lerouxb/minor-1/firmware/attiny3216/include/avr/iotn3216.h

/*
 * Copyright (C) 2020, Microchip Technology Inc. and its subsidiaries ("Microchip")
 * All rights reserved.
 *
 * This software is developed by Microchip Technology Inc. and its subsidiaries ("Microchip").
 *
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
 *     3. Microchip's name may not be used to endorse or promote products derived from this
 *        software without specific prior written permission.
 *
 * THIS SOFTWARE IS PROVIDED BY MICROCHIP "AS IS" AND ANY EXPRESS OR IMPLIED WARRANTIES,
 * INCLUDING, BUT NOT LIMITED TO, THE IMPLIED WARRANTIES OF MERCHANTABILITY AND FITNESS FOR
 * PURPOSE ARE DISCLAIMED.  IN NO EVENT SHALL MICROCHIP BE LIABLE FOR ANY DIRECT, INDIRECT,
 * INCIDENTAL, SPECIAL, EXEMPLARY, OR CONSEQUENTIAL DAMAGES (INCLUDING BUT NOT LIMITED TO
 * PROCUREMENT OF SUBSTITUTE GOODS OR SERVICES; LOSS OF USE, DATA OR PROFITS; OR BUSINESS
 * INTERRUPTION) HOWSOEVER CAUSED AND ON ANY THEORY OF LIABILITY, WHETHER IN CONTRACT, STRICT
 * LIABILITY, OR TORT (INCLUDING NEGLIGENCE OR OTHERWISE) ARISING IN ANY WAY OUT OF THE USE OF
 * THIS SOFTWARE, EVEN IF ADVISED OF THE POSSIBILITY OF SUCH DAMAGE.
 */

#ifndef _AVR_IO_H_
#error "Include <avr/io.h> instead of this file."
#endif

#ifndef _AVR_IOXXX_H_
#define _AVR_IOXXX_H_ "iotn3216.h"
#else
#error "Attempt to include more than one <avr/ioXXX.h> file."
#endif

#ifndef _AVR_ATTINY3216_H_INCLUDED
#define _AVR_ATTINY3216_H_INCLUDED

/* Ungrouped common registers */
#define CCP _SFR_MEM8(0x0034)  /* Configuration Change Protection */
#define SPH _SFR_MEM8(0x003E)  /* Stack Pointer High */
#define SPL _SFR_MEM8(0x003D)  /* Stack Pointer Low */
#define SREG _SFR_MEM8(0x003F) /* Status Register */

#define GPIOR0 _SFR_MEM8(0x001C) /* General Purpose IO Register 0 */
#define GPIOR1 _SFR_MEM8(0x001D) /* General Purpose IO Register 1 */
#define GPIOR2 _SFR_MEM8(0x001E) /* General Purpose IO Register 2 */
#define GPIOR3 _SFR_MEM8(0x001F) /* General Purpose IO Register 3 */

/* Deprecated */
#define GPIO0 _SFR_MEM8(0x001C) /* General Purpose IO Register 0 */
#define GPIO1 _SFR_MEM8(0x001D) /* General Purpose IO Register 1 */
#define GPIO2 _SFR_MEM8(0x001E) /* General Purpose IO Register 2 */
#define GPIO3 _SFR_MEM8(0x001F) /* General Purpose IO Register 3 */

/* C Language Only */
#if !defined(__ASSEMBLER__)

#include <stdint.h>

typedef volatile uint8_t  register8_t;
typedef volatile uint16_t register16_t;
typedef volatile uint32_t register32_t;

#ifdef _WORDREGISTER
#undef _WORDREGISTER
#endif
#define _WORDREGISTER(regname)                                                                                         \
	__extension__ union {                                                                                              \
		register16_t regname;                                                                                          \
		struct {                                                                                                       \
			register8_t regname##L;                                                                                    \
			register8_t regname##H;                                                                                    \
		};                                                                                                             \
	}

#ifdef _DWORDREGISTER
#undef _DWORDREGISTER
#endif
#define _DWORDREGISTER(regname)                                                                                        \
	__extension__ union {                                                                                              \
		register32_t regname;                                                                                          \
		struct {                                                                                                       \
			register8_t regname##0;                                                                                    \
			register8_t regname##1;                                                                                    \
			register8_t regname##2;                                                                                    \
			register8_t regname##3;                                                                                    \
		};                                                                                                             \
	}

/*
==========================================================================
IO Module Structures
==========================================================================
*/

/*
--------------------------------------------------------------------------
AC - Analog Comparator
--------------------------------------------------------------------------
*/

/* Analog Comparator */
typedef struct AC_struct {
	register8_t CTRLA; /* Control A */
	register8_t reserved_1[1];
	register8_t MUXCTRLA; /* Mux Control A */
	register8_t reserved_2[3];
	register8_t INTCTRL; /* Interrupt Control */
	register8_t STATUS;  /* Status */
} AC_t;

/* Hysteresis Mode select */
typedef enum AC_HYSMODE_enum {
	AC_HYSMODE_OFF_gc  = (0x00 << 1), /* No hysteresis */
	AC_HYSMODE_10mV_gc = (0x01 << 1), /* 10mV hysteresis */
	AC_HYSMODE_25mV_gc = (0x02 << 1), /* 25mV hysteresis */
	AC_HYSMODE_50mV_gc = (0x03 << 1), /* 50mV hysteresis */
} AC_HYSMODE_t;

/* Interrupt Mode select */
typedef enum AC_INTMODE_enum {
	AC_INTMODE_BOTHEDGE_gc = (0x00 << 4), /* Any Edge */
	AC_INTMODE_NEGEDGE_gc  = (0x02 << 4), /* Negative Edge */
	AC_INTMODE_POSEDGE_gc  = (0x03 << 4), /* Positive Edge */
} AC_INTMODE_t;

/* Low Power Mode select */
typedef enum AC_LPMODE_enum {
	AC_LPMODE_DIS_gc = (0x00 << 3), /* Low power mode disabled */
	AC_LPMODE_EN_gc  = (0x01 << 3), /* Low power mode enabled */
} AC_LPMODE_t;

/* Negative Input MUX Selection select */
typedef enum AC_MUXNEG_enum {
	AC_MUXNEG_PIN0_gc = (0x00 << 0), /* Negative Pin 0 */
	AC_MUXNEG_PIN1_gc = (0x01 << 0), /* Negative Pin 1 */
	AC_MUXNEG_VREF_gc = (0x02 << 0), /* Voltage Reference */
	AC_MUXNEG_DAC_gc  = (0x03 << 0), /* DAC output */
} AC_MUXNEG_t;

/* Positive Input MUX Selection select */
typedef enum AC_MUXPOS_enum {
	AC_MUXPOS_PIN0_gc = (0x00 << 3), /* Positive Pin 0 */
	AC_MUXPOS_PIN1_gc = (0x01 << 3), /* Positive Pin 1 */
	AC_MUXPOS_PIN2_gc = (0x02 << 3), /* Positive Pin 2 */
	AC_MUXPOS_PIN3_gc = (0x03 << 3), /* Positive Pin 3 */
} AC_MUXPOS_t;

/*
--------------------------------------------------------------------------
ADC - Analog to Digital Converter
--------------------------------------------------------------------------
*/

/* Analog to Digital Converter */
typedef struct ADC_struct {
	register8_t CTRLA;    /* Control A */
	register8_t CTRLB;    /* Control B */
	register8_t CTRLC;    /* Control C */
	register8_t CTRLD;    /* Control D */
	register8_t CTRLE;    /* Control E */
	register8_t SAMPCTRL; /* Sample Control */
	register8_t MUXPOS;   /* Positive mux input */
	register8_t reserved_1[1];
	register8_t COMMAND;  /* Command */
	register8_t EVCTRL;   /* Event Control */
	register8_t INTCTRL;  /* Interrupt Control */
	register8_t INTFLAGS; /* Interrupt Flags */
	register8_t DBGCTRL;  /* Debug Control */
	register8_t TEMP;     /* Temporary Data */
	register8_t reserved_2[2];
	_WORDREGISTER(RES);   /* ADC Accumulator Result */
	_WORDREGISTER(WINLT); /* Window comparator low threshold */
	_WORDREGISTER(WINHT); /* Window comparator high threshold */
	register8_t CALIB;    /* Calibration */
	register8_t reserved_3[1];
} ADC_t;

/* Automatic Sampling Delay Variation select */
typedef enum ADC_ASDV_enum {
	ADC_ASDV_ASVOFF_gc = (0x00 << 4), /* The Automatic Sampling Delay Variation is disabled */
	ADC_ASDV_ASVON_gc  = (0x01 << 4), /* The Automatic Sampling Delay Variation is enabled */
} ADC_ASDV_t;

/* Duty Cycle select */
typedef enum ADC_DUTYCYC_enum {
	ADC_DUTYCYC_DUTY50_gc = (0x00 << 0), /* 50% Duty cycle */
	ADC_DUTYCYC_DUTY25_gc = (0x01 << 0), /* 25% Duty cycle */
} ADC_DUTYCYC_t;

/* Initial Delay Selection select */
typedef enum ADC_INITDLY_enum {
	ADC_INITDLY_DLY0_gc   = (0x00 << 5), /* Delay 0 CLK_ADC cycles */
	ADC_INITDLY_DLY16_gc  = (0x01 << 5), /* Delay 16 CLK_ADC cycles */
	ADC_INITDLY_DLY32_gc  = (0x02 << 5), /* Delay 32 CLK_ADC cycles */
	ADC_INITDLY_DLY64_gc  = (0x03 << 5), /* Delay 64 CLK_ADC cycles */
	ADC_INITDLY_DLY128_gc = (0x04 << 5), /* Delay 128 CLK_ADC cycles */
	ADC_INITDLY_DLY256_gc = (0x05 << 5), /* Delay 256 CLK_ADC cycles */
} ADC_INITDLY_t;

/* Analog Channel Selection Bits select */
typedef enum ADC_MUXPOS_enum {
	ADC_MUXPOS_AIN0_gc      = (0x00 << 0), /* ADC input pin 0 */
	ADC_MUXPOS_AIN1_gc      = (0x01 << 0), /* ADC input pin 1 */
	ADC_MUXPOS_AIN2_gc      = (0x02 << 0), /* ADC input pin 2 */
	ADC_MUXPOS_AIN3_gc      = (0x03 << 0), /* ADC input pin 3 */
	ADC_MUXPOS_AIN4_gc      = (0x04 << 0), /* ADC input pin 4 */
	ADC_MUXPOS_AIN5_gc      = (0x05 << 0), /* ADC input pin 5 */
	ADC_MUXPOS_AIN6_gc      = (0x06 << 0), /* ADC input pin 6 */
	ADC_MUXPOS_AIN7_gc      = (0x07 << 0), /* ADC input pin 7 */
	ADC_MUXPOS_AIN8_gc      = (0x08 << 0), /* ADC input pin 8 */
	ADC_MUXPOS_AIN9_gc      = (0x09 << 0), /* ADC input pin 9 */
	ADC_MUXPOS_AIN10_gc     = (0x0A << 0), /* ADC input pin 10 */
	ADC_MUXPOS_AIN11_gc     = (0x0B << 0), /* ADC input pin 11 */
	ADC_MUXPOS_PTC_gc       = (0x1B << 0), /* PTC/DAC2 */
	ADC_MUXPOS_DAC0_gc      = (0x1C << 0), /* DAC0/DAC0 */
	ADC_MUXPOS_INTREF_gc    = (0x1D << 0), /* Internal Ref */
	ADC_MUXPOS_TEMPSENSE_gc = (0x1E << 0), /* Temp sensor/DAC1 */
	ADC_MUXPOS_GND_gc       = (0x1F << 0), /* GND */
} ADC_MUXPOS_t;

/* Clock Pre-scaler select */
typedef enum ADC_PRESC_enum {
	ADC_PRESC_DIV2_gc   = (0x00 << 0), /* CLK_PER divided by 2 */
	ADC_PRESC_DIV4_gc   = (0x01 << 0), /* CLK_PER divided by 4 */
	ADC_PRESC_DIV8_gc   = (0x02 << 0), /* CLK_PER divided by 8 */
	ADC_PRESC_DIV16_gc  = (0x03 << 0), /* CLK_PER divided by 16 */
	ADC_PRESC_DIV32_gc  = (0x04 << 0), /* CLK_PER divided by 32 */
	ADC_PRESC_DIV64_gc  = (0x05 << 0), /* CLK_PER divided by 64 */
	ADC_PRESC_DIV128_gc = (0x06 << 0), /* CLK_PER divided by 128 */
	ADC_PRESC_DIV256_gc = (0x07 << 0), /* CLK_PER divided by 256 */
} ADC_PRESC_t;

/* Reference Selection select */
typedef enum ADC_REFSEL_enum {
	ADC_REFSEL_INTREF_gc = (0x00 << 4), /* Internal reference */
	ADC_REFSEL_VDDREF_gc = (0x01 << 4), /* VDD */
	ADC_REFSEL_VREFA_gc  = (0x02 << 4), /* External reference */
} ADC_REFSEL_t;

/* ADC Resolution select */
typedef enum ADC_RESSEL_enum {
	ADC_RESSEL_10BIT_gc = (0x00 << 2), /* 10-bit mode */
	ADC_RESSEL_8BIT_gc  = (0x01 << 2), /* 8-bit mode */
} ADC_RESSEL_t;

/* Accumulation Samples select */
typedef enum ADC_SAMPNUM_enum {
	ADC_SAMPNUM_ACC1_gc  = (0x00 << 0), /* 1 ADC sample */
	ADC_SAMPNUM_ACC2_gc  = (0x01 << 0), /* Accumulate 2 samples */
	ADC_SAMPNUM_ACC4_gc  = (0x02 << 0), /* Accumulate 4 samples */
	ADC_SAMPNUM_ACC8_gc  = (0x03 << 0), /* Accumulate 8 samples */
	ADC_SAMPNUM_ACC16_gc = (0x04 << 0), /* Accumulate 16 samples */
	ADC_SAMPNUM_ACC32_gc = (0x05 << 0), /* Accumulate 32 samples */
	ADC_SAMPNUM_ACC64_gc = (0x06 << 0), /* Accumulate 64 samples */
} ADC_SAMPNUM_t;

/* Window Comparator Mode select */
typedef enum ADC_WINCM_enum {
	ADC_WINCM_NONE_gc    = (0x00 << 0), /* No Window Comparison */
	ADC_WINCM_BELOW_gc   = (0x01 << 0), /* Below Window */
	ADC_WINCM_ABOVE_gc   = (0x02 << 0), /* Above Window */
	ADC_WINCM_INSIDE_gc  = (0x03 << 0), /* Inside Window */
	ADC_WINCM_OUTSIDE_gc = (0x04 << 0), /* Outside Window */
} ADC_WINCM_t;

/*
--------------------------------------------------------------------------
BOD - Bod interface
--------------------------------------------------------------------------
*/

/* Bod interface */
typedef struct BOD_struct {
	register8_t CTRLA; /* Control A */
	register8_t CTRLB; /* Control B */
	register8_t reserved_1[6];
	register8_t VLMCTRLA; /* Voltage level monitor Control */
	register8_t INTCTRL;  /* Voltage level monitor interrupt Control */
	register8_t INTFLAGS; /* Voltage level monitor interrupt Flags */
	register8_t STATUS;   /* Voltage level monitor status */
	register8_t reserved_2[4];
} BOD_t;

/* Operation in active mode select */
typedef enum BOD_ACTIVE_enum {
	BOD_ACTIVE_DIS_gc     = (0x00 << 2), /* Disabled */
	BOD_ACTIVE_ENABLED_gc = (0x01 << 2), /* Enabled */
	BOD_ACTIVE_SAMPLED_gc = (0x02 << 2), /* Sampled */
	BOD_ACTIVE_ENWAKE_gc  = (0x03 << 2), /* Enabled with wake-up halted until BOD is ready */
} BOD_ACTIVE_t;

/* Bod level select */
typedef enum BOD_LVL_enum {
	BOD_LVL_BODLEVEL0_gc = (0x00 << 0), /* 1.8 V */
	BOD_LVL_BODLEVEL2_gc = (0x02 << 0), /* 2.6 V */
	BOD_LVL_BODLEVEL7_gc = (0x07 << 0), /* 4.2 V */
} BOD_LVL_t;

/* Sample frequency select */
typedef enum BOD_SAMPFREQ_enum {
	BOD_SAMPFREQ_1KHZ_gc  = (0x00 << 4), /* 1kHz sampling frequency */
	BOD_SAMPFREQ_125HZ_gc = (0x01 << 4), /* 125Hz sampling frequency */
} BOD_SAMPFREQ_t;

/* Operation in sleep mode select */
typedef enum BOD_SLEEP_enum {
	BOD_SLEEP_DIS_gc     = (0x00 << 0), /* Disabled */
	BOD_SLEEP_ENABLED_gc = (0x01 << 0), /* Enabled */
	BOD_SLEEP_SAMPLED_gc = (0x02 << 0), /* Sampled */
} BOD_SLEEP_t;

/* Configuration select */
typedef enum BOD_VLMCFG_enum {
	BOD_VLMCFG_BELOW_gc = (0x00 << 1), /* Interrupt when supply goes below VLM level */
	BOD_VLMCFG_ABOVE_gc = (0x01 << 1), /* Interrupt when supply goes above VLM level */
	BOD_VLMCFG_CROSS_gc = (0x02 << 1), /* Interrupt when supply crosses VLM level */
} BOD_VLMCFG_t;

/* voltage level monitor level select */
typedef enum BOD_VLMLVL_enum {
	BOD_VLMLVL_5ABOVE_gc  = (0x00 << 0), /* VLM threshold 5% above BOD level */
	BOD_VLMLVL_15ABOVE_gc = (0x01 << 0), /* VLM threshold 15% above BOD level */
	BOD_VLMLVL_25ABOVE_gc = (0x02 << 0), /* VLM threshold 25% above BOD level */
} BOD_VLMLVL_t;

/*
--------------------------------------------------------------------------
CCL - Configurable Custom Logic
--------------------------------------------------------------------------
*/

/* Configurable Custom Logic */
typedef struct CCL_struct {
	register8_t CTRLA;    /* Control Register A */
	register8_t SEQCTRL0; /* Sequential Control 0 */
	register8_t reserved_1[3];
	register8_t LUT0CTRLA; /* LUT Control 0 A */
	register8_t LUT0CTRLB; /* LUT Control 0 B */
	register8_t LUT0CTRLC; /* LUT Control 0 C */
	register8_t TRUTH0;    /* Truth 0 */
	register8_t LUT1CTRLA; /* LUT Control 1 A */
	register8_t LUT1CTRLB; /* LUT Control 1 B */
	register8_t LUT1CTRLC; /* LUT Control 1 C */
	register8_t TRUTH1;    /* Truth 1 */
	register8_t reserved_2[51];
} CCL_t;

/* Edge Detection Enable select */
typedef enum CCL_EDGEDET_enum {
	CCL_EDGEDET_DIS_gc = (0x00 << 7), /* Edge detector is disabled */
	CCL_EDGEDET_EN_gc  = (0x01 << 7), /* Edge detector is enabled */
} CCL_EDGEDET_t;

/* Filter Selection select */
typedef enum CCL_FILTSEL_enum {
	CCL_FILTSEL_DISABLE_gc = (0x00 << 4), /* Filter disabled */
	CCL_FILTSEL_SYNCH_gc   = (0x01 << 4), /* Synchronizer enabled */
	CCL_FILTSEL_FILTER_gc  = (0x02 << 4), /* Filter enabled */
} CCL_FILTSEL_t;

/* LUT Input 0 Source Selection select */
typedef enum CCL_INSEL0_enum {
	CCL_INSEL0_MASK_gc     = (0x00 << 0), /* Masked input */
	CCL_INSEL0_FEEDBACK_gc = (0x01 << 0), /* Feedback input source */
	CCL_INSEL0_LINK_gc     = (0x02 << 0), /* Linked LUT input source */
	CCL_INSEL0_EVENT0_gc   = (0x03 << 0), /* Event input source 0 */
	CCL_INSEL0_EVENT1_gc   = (0x04 << 0), /* Event input source 1 */
	CCL_INSEL0_IO_gc       = (0x05 << 0), /* IO pin LUTn-IN0 input source */
	CCL_INSEL0_AC0_gc      = (0x06 << 0), /* AC0 OUT input source */
	CCL_INSEL0_TCB0_gc     = (0x07 << 0), /* TCB0 WO input source */
	CCL_INSEL0_TCA0_gc     = (0x08 << 0), /* TCA0 WO0 input source */
	CCL_INSEL0_TCD0_gc     = (0x09 << 0), /* TCD0 WOA input source */
	CCL_INSEL0_USART0_gc   = (0x0A << 0), /* USART0 XCK input source */
	CCL_INSEL0_SPI0_gc     = (0x0B << 0), /* SPI0 SCK source */
	CCL_INSEL0_AC1_gc      = (0x0C << 0), /* AC1 OUT input source */
	CCL_INSEL0_TCB1_gc     = (0x0D << 0), /* TCB1 WO input source */
	CCL_INSEL0_AC2_gc      = (0x0E << 0), /* AC2 OUT input source */
} CCL_INSEL0_t;

/* LUT Input 1 Source Selection select */
typedef enum CCL_INSEL1_enum {
	CCL_INSEL1_MASK_gc     = (0x00 << 4), /* Masked input */
	CCL_INSEL1_FEEDBACK_gc = (0x01 << 4), /* Feedback input source */
	CCL_INSEL1_LINK_gc     = (0x02 << 4), /* Linked LUT input source */
	CCL_INSEL1_EVENT0_gc   = (0x03 << 4), /* Event input source 0 */
	CCL_INSEL1_EVENT1_gc   = (0x04 << 4), /* Event input source 1 */
	CCL_INSEL1_IO_gc       = (0x05 << 4), /* IO pin LUTn-N1 input source */
	CCL_INSEL1_AC0_gc      = (0x06 << 4), /* AC0 OUT input source */
	CCL_INSEL1_TCB0_gc     = (0x07 << 4), /* TCB0 WO input source */
	CCL_INSEL1_TCA0_gc     = (0x08 << 4), /* TCA0 WO1 input source */
	CCL_INSEL1_TCD0_gc     = (0x09 << 4), /* TCD0 WOB input source */
	CCL_INSEL1_USART0_gc   = (0x0A << 4), /* USART0 TXD input source */
	CCL_INSEL1_SPI0_gc     = (0x0B << 4), /* SPI0 MOSI input source */
	CCL_INSEL1_AC1_gc      = (0x0C << 4), /* AC1 OUT input source */
	CCL_INSEL1_TCB1_gc     = (0x0D << 4), /* TCB1 WO input source */
	CCL_INSEL1_AC2_gc      = (0x0E << 4), /* AC2 OUT input source */
} CCL_INSEL1_t;

/* LUT Input 2 Source Selection select */
typedef enum CCL_INSEL2_enum {
	CCL_INSEL2_MASK_gc     = (0x00 << 0), /* Masked input */
	CCL_INSEL2_FEEDBACK_gc = (0x01 << 0), /* Feedback input source */
	CCL_INSEL2_LINK_gc     = (0x02 << 0), /* Linked LUT input source */
	CCL_INSEL2_EVENT0_gc   = (0x03 << 0), /* Event input source 0 */
	CCL_INSEL2_EVENT1_gc   = (0x04 << 0), /* Event input source 1 */
	CCL_INSEL2_IO_gc       = (0x05 << 0), /* IO pin LUTn-IN2 input source */
	CCL_INSEL2_AC0_gc      = (0x06 << 0), /* AC0 OUT input source */
	CCL_INSEL2_TCB0_gc     = (0x07 << 0), /* TCB0 WO input source */
	CCL_INSEL2_TCA0_gc     = (0x08 << 0), /* TCA0 WO2 input source */
	CCL_INSEL2_TCD0_gc     = (0x09 << 0), /* TCD0 WOA input source */
	CCL_INSEL2_SPI0_gc     = (0x0B << 0), /* SPI0 MISO source */
	CCL_INSEL2_AC1_gc      = (0x0C << 0), /* AC1 OUT input source */
	CCL_INSEL2_TCB1_gc     = (0x0D << 0), /* TCB1 WO input source */
	CCL_INSEL2_AC2_gc      = (0x0E << 0), /* AC2 OUT input source */
} CCL_INSEL2_t;

/* Sequential Selection select */
typedef enum CCL_SEQSEL_enum {
	CCL_SEQSEL_DISABLE_gc = (0x00 << 0), /* Sequential logic disabled */
	CCL_SEQSEL_DFF_gc     = (0x01 << 0), /* D FlipFlop */
	CCL_SEQSEL_JK_gc      = (0x02 << 0), /* JK FlipFlop */
	CCL_SEQSEL_LATCH_gc   = (0x03 << 0), /* D Latch */
	CCL_SEQSEL_RS_gc      = (0x04 << 0), /* RS Latch */
} CCL_SEQSEL_t;

/*
--------------------------------------------------------------------------
CLKCTRL - Clock controller
--------------------------------------------------------------------------
*/

/* Clock controller */
typedef struct CLKCTRL_struct {
	register8_t MCLKCTRLA;  /* MCLK Control A */
	register8_t MCLKCTRLB;  /* MCLK Control B */
	register8_t MCLKLOCK;   /* MCLK Lock */
	register8_t MCLKSTATUS; /* MCLK Status */
	register8_t reserved_1[12];
	register8_t OSC20MCTRLA;  /* OSC20M Control A */
	register8_t OSC20MCALIBA; /* OSC20M Calibration A */
	register8_t OSC20MCALIBB; /* OSC20M Calibration B */
	register8_t reserved_2[5];
	register8_t OSC32KCTRLA; /* OSC32K Control A */
	register8_t reserved_3[3];
	register8_t XOSC32KCTRLA; /* XOSC32K Control A */
	register8_t reserved_4[3];
} CLKCTRL_t;

/* clock select select */
typedef enum CLKCTRL_CLKSEL_enum {
	CLKCTRL_CLKSEL_OSC20M_gc    = (0x00 << 0), /* 20MHz internal oscillator */
	CLKCTRL_CLKSEL_OSCULP32K_gc = (0x01 << 0), /* 32KHz internal Ultra Low Power oscillator */
	CLKCTRL_CLKSEL_XOSC32K_gc   = (0x02 << 0), /* 32.768kHz external crystal oscillator */
	CLKCTRL_CLKSEL_EXTCLK_gc    = (0x03 << 0), /* External clock */
} CLKCTRL_CLKSEL_t;

/* Crystal startup time select */
typedef enum CLKCTRL_CSUT_enum {
	CLKCTRL_CSUT_1K_gc  = (0x00 << 4), /* 1K cycles */
	CLKCTRL_CSUT_16K_gc = (0x01 << 4), /* 16K cycles */
	CLKCTRL_CSUT_32K_gc = (0x02 << 4), /* 32K cycles */
	CLKCTRL_CSUT_64K_gc = (0x03 << 4), /* 64K cycles */
} CLKCTRL_CSUT_t;

/* Prescaler division select */
typedef enum CLKCTRL_PDIV_enum {
	CLKCTRL_PDIV_2X_gc  = (0x00 << 1), /* 2X */
	CLKCTRL_PDIV_4X_gc  = (0x01 << 1), /* 4X */
	CLKCTRL_PDIV_8X_gc  = (0x02 << 1), /* 8X */
	CLKCTRL_PDIV_16X_gc = (0x03 << 1), /* 16X */
	CLKCTRL_PDIV_32X_gc = (0x04 << 1), /* 32X */
	CLKCTRL_PDIV_64X_gc = (0x05 << 1), /* 64X */
	CLKCTRL_PDIV_6X_gc  = (0x08 << 1), /* 6X */
	CLKCTRL_PDIV_10X_gc = (0x09 << 1), /* 10X */
	CLKCTRL_PDIV_12X_gc = (0x0A << 1), /* 12X */
	CLKCTRL_PDIV_24X_gc = (0x0B << 1), /* 24X */
	CLKCTRL_PDIV_48X_gc = (0x0C << 1), /* 48X */
} CLKCTRL_PDIV_t;

/*
--------------------------------------------------------------------------
CPU - CPU
--------------------------------------------------------------------------
*/

/* CCP signature select */
typedef enum CCP_enum {
	CCP_SPM_gc   = (0x9D << 0), /* SPM Instruction Protection */
	CCP_IOREG_gc = (0xD8 << 0), /* IO Register Protection */
} CCP_t;

/*
--------------------------------------------------------------------------
CPUINT - Interrupt Controller
--------------------------------------------------------------------------
*/

/* Interrupt Controller */
typedef struct CPUINT_struct {
	register8_t CTRLA;   /* Control A */
	register8_t STATUS;  /* Status */
	register8_t LVL0PRI; /* Interrupt Level 0 Priority */
	register8_t LVL1VEC; /* Interrupt Level 1 Priority Vector */
} CPUINT_t;

/*
--------------------------------------------------------------------------
CRCSCAN - CRCSCAN
--------------------------------------------------------------------------
*/

/* CRCSCAN */
typedef struct CRCSCAN_struct {
	register8_t CTRLA;  /* Control A */
	register8_t CTRLB;  /* Control B */
	register8_t STATUS; /* Status */
	register8_t reserved_1[1];
} CRCSCAN_t;

/* CRC Source select */
typedef enum CRCSCAN_SRC_enum {
	CRCSCAN_SRC_FLASH_gc       = (0x00 << 0), /* CRC on entire flash */
	CRCSCAN_SRC_APPLICATION_gc = (0x01 << 0), /* CRC on boot and appl section of flash */
	CRCSCAN_SRC_BOOT_gc        = (0x02 << 0), /* CRC on boot section of flash */
} CRCSCAN_SRC_t;

/*
--------------------------------------------------------------------------
DAC - Digital to Analog Converter
--------------------------------------------------------------------------
*/

/* Digital to Analog Converter */
typedef struct DAC_struct {
	register8_t CTRLA; /* Control Register A */
	register8_t DATA;  /* DATA Register */
	register8_t reserved_1[2];
} DAC_t;

/*
--------------------------------------------------------------------------
EVSYS - Event System
--------------------------------------------------------------------------
*/

/* Event System */
typedef struct EVSYS_struct {
	register8_t ASYNCSTROBE; /* Asynchronous Channel Strobe */
	register8_t SYNCSTROBE;  /* Synchronous Channel Strobe */
	register8_t ASYNCCH0;    /* Asynchronous Channel 0 Generator Selection */
	register8_t ASYNCCH1;    /* Asynchronous Channel 1 Generator Selection */
	register8_t ASYNCCH2;    /* Asynchronous Channel 2 Generator Selection */
	register8_t ASYNCCH3;    /* Asynchronous Channel 3 Generator Selection */
	register8_t reserved_1[4];
	register8_t SYNCCH0; /* Synchronous Channel 0 Generator Selection */
	register8_t SYNCCH1; /* Synchronous Channel 1 Generator Selection */
	register8_t reserved_2[6];
	register8_t ASYNCUSER0;  /* Asynchronous User Ch 0 Input Selection - TCB0 */
	register8_t ASYNCUSER1;  /* Asynchronous User Ch 1 Input Selection - ADC0 */
	register8_t ASYNCUSER2;  /* Asynchronous User Ch 2 Input Selection - CCL LUT0 Event 0 */
	register8_t ASYNCUSER3;  /* Asynchronous User Ch 3 Input Selection - CCL LUT1 Event 0 */
	register8_t ASYNCUSER4;  /* Asynchronous User Ch 4 Input Selection - CCL LUT0 Event 1 */
	register8_t ASYNCUSER5;  /* Asynchronous User Ch 5 Input Selection - CCL LUT1 Event 1 */
	register8_t ASYNCUSER6;  /* Asynchronous User Ch 6 Input Selection - TCD0 Event 0 */
	register8_t ASYNCUSER7;  /* Asynchronous User Ch 7 Input Selection - TCD0 Event 1 */
	register8_t ASYNCUSER8;  /* Asynchronous User Ch 8 Input Selection - Event Out 0 */
	register8_t ASYNCUSER9;  /* Asynchronous User Ch 9 Input Selection - Event Out 1 */
	register8_t ASYNCUSER10; /* Asynchronous User Ch 10 Input Selection - Event Out 2 */
	register8_t ASYNCUSER11; /* Asynchronous User Ch 11 Input Selection - TCB1 */
	register8_t ASYNCUSER12; /* Asynchronous User Ch 12 Input Selection - ADC1 */
	register8_t reserved_3[3];
	register8_t SYNCUSER0; /* Synchronous User Ch 0 - TCA0 */
	register8_t SYNCUSER1; /* Synchronous User Ch 1 - USART0 */
	register8_t reserved_4[28];
} EVSYS_t;

/* Asynchronous Channel 0 Generator Selection select */
typedef enum EVSYS_ASYNCCH0_enum {
	EVSYS_ASYNCCH0_OFF_gc          = (0x00 << 0), /* Off */
	EVSYS_ASYNCCH0_CCL_LUT0_gc     = (0x01 << 0), /* Configurable Custom Logic LUT0 */
	EVSYS_ASYNCCH0_CCL_LUT1_gc     = (0x02 << 0), /* Configurable Custom Logic LUT1 */
	EVSYS_ASYNCCH0_AC0_OUT_gc      = (0x03 << 0), /* Analog Comparator 0 out */
	EVSYS_ASYNCCH0_TCD0_CMPBCLR_gc = (0x04 << 0), /* Timer/Counter D0 compare B clear */
	EVSYS_ASYNCCH0_TCD0_CMPASET_gc = (0x05 << 0), /* Timer/Counter D0 compare A set */
	EVSYS_ASYNCCH0_TCD0_CMPBSET_gc = (0x06 << 0), /* Timer/Counter D0 compare B set */
	EVSYS_ASYNCCH0_TCD0_PROGEV_gc  = (0x07 << 0), /* Timer/Counter D0 program event */
	EVSYS_ASYNCCH0_RTC_OVF_gc      = (0x08 << 0), /* Real Time Counter overflow */
	EVSYS_ASYNCCH0_RTC_CMP_gc      = (0x09 << 0), /* Real Time Counter compare */
	EVSYS_ASYNCCH0_PORTA_PIN0_gc   = (0x0A << 0), /* Asynchronous Event from Pin PA0 */
	EVSYS_ASYNCCH0_PORTA_PIN1_gc   = (0x0B << 0), /* Asynchronous Event from Pin PA1 */
	EVSYS_ASYNCCH0_PORTA_PIN2_gc   = (0x0C << 0), /* Asynchronous Event from Pin PA2 */
	EVSYS_ASYNCCH0_PORTA_PIN3_gc   = (0x0D << 0), /* Asynchronous Event from Pin PA3 */
	EVSYS_ASYNCCH0_PORTA_PIN4_gc   = (0x0E << 0), /* Asynchronous Event from Pin PA4 */
	EVSYS_ASYNCCH0_PORTA_PIN5_gc   = (0x0F << 0), /* Asynchronous Event from Pin PA5 */
	EVSYS_ASYNCCH0_PORTA_PIN6_gc   = (0x10 << 0), /* Asynchronous Event from Pin PA6 */
	EVSYS_ASYNCCH0_PORTA_PIN7_gc   = (0x11 << 0), /* Asynchronous Event from Pin PA7 */
	EVSYS_ASYNCCH0_UPDI_gc         = (0x12 << 0), /* Unified Program and debug interface */
	EVSYS_ASYNCCH0_AC1_OUT_gc      = (0x13 << 0), /* Analog Comparator 1 out */
	EVSYS_ASYNCCH0_AC2_OUT_gc      = (0x14 << 0), /* Analog Comparator 2 out */
} EVSYS_ASYNCCH0_t;

/* Asynchronous Channel 1 Generator Selection select */
typedef enum EVSYS_ASYNCCH1_enum {
	EVSYS_ASYNCCH1_OFF_gc          = (0x00 << 0), /* Off */
	EVSYS_ASYNCCH1_CCL_LUT0_gc     = (0x01 << 0), /* Configurable custom logic LUT0 */
	EVSYS_ASYNCCH1_CCL_LUT1_gc     = (0x02 << 0), /* Configurable custom logic LUT1 */
	EVSYS_ASYNCCH1_AC0_OUT_gc      = (0x03 << 0), /* Analog Comparator 0 out */
	EVSYS_ASYNCCH1_TCD0_CMPBCLR_gc = (0x04 << 0), /* Timer/Counter D0 compare B clear */
	EVSYS_ASYNCCH1_TCD0_CMPASET_gc = (0x05 << 0), /* Timer/Counter D0 compare A set */
	EVSYS_ASYNCCH1_TCD0_CMPBSET_gc = (0x06 << 0), /* Timer/Counter D0 compare B set */
	EVSYS_ASYNCCH1_TCD0_PROGEV_gc  = (0x07 << 0), /* Timer/Counter D0 program event */
	EVSYS_ASYNCCH1_RTC_OVF_gc      = (0x08 << 0), /* Real Time Counter overflow */
	EVSYS_ASYNCCH1_RTC_CMP_gc      = (0x09 << 0), /* Real Time Counter compare */
	EVSYS_ASYNCCH1_PORTB_PIN0_gc   = (0x0A << 0), /* Asynchronous Event from Pin PB0 */
	EVSYS_ASYNCCH1_PORTB_PIN1_gc   = (0x0B << 0), /* Asynchronous Event from Pin PB1 */
	EVSYS_ASYNCCH1_PORTB_PIN2_gc   = (0x0C << 0), /* Asynchronous Event from Pin PB2 */
	EVSYS_ASYNCCH1_PORTB_PIN3_gc   = (0x0D << 0), /* Asynchronous Event from Pin PB3 */
	EVSYS_ASYNCCH1_PORTB_PIN4_gc   = (0x0E << 0), /* Asynchronous Event from Pin PB4 */
	EVSYS_ASYNCCH1_PORTB_PIN5_gc   = (0x0F << 0), /* Asynchronous Event from Pin PB5 */
	EVSYS_ASYNCCH1_PORTB_PIN6_gc   = (0x10 << 0), /* Asynchronous Event from Pin PB6 */
	EVSYS_ASYNCCH1_PORTB_PIN7_gc   = (0x11 << 0), /* Asynchronous Event from Pin PB7 */
	EVSYS_ASYNCCH1_AC1_OUT_gc      = (0x12 << 0), /* Analog Comparator 1 out */
	EVSYS_ASYNCCH1_AC2_OUT_gc      = (0x13 << 0), /* Analog Comparator 2 out */
} EVSYS_ASYNCCH1_t;

/* Asynchronous Channel 2 Generator Selection select */
typedef enum EVSYS_ASYNCCH2_enum {
	EVSYS_ASYNCCH2_OFF_gc          = (0x00 << 0), /* Off */
	EVSYS_ASYNCCH2_CCL_LUT0_gc     = (0x01 << 0), /* Configurable Custom Logic LUT0 */
	EVSYS_ASYNCCH2_CCL_LUT1_gc     = (0x02 << 0), /* Configurable Custom Logic LUT1 */
	EVSYS_ASYNCCH2_AC0_OUT_gc      = (0x03 << 0), /* Analog Comparator 0 out */
	EVSYS_ASYNCCH2_TCD0_CMPBCLR_gc = (0x04 << 0), /* Timer/Counter D0 compare B clear */
	EVSYS_ASYNCCH2_TCD0_CMPASET_gc = (0x05 << 0), /* Timer/Counter D0 compare A set */
	EVSYS_ASYNCCH2_TCD0_CMPBSET_gc = (0x06 << 0), /* Timer/Counter D0 compare B set */
	EVSYS_ASYNCCH2_TCD0_PROGEV_gc  = (0x07 << 0), /* Timer/Counter D0 program event */
	EVSYS_ASYNCCH2_RTC_OVF_gc      = (0x08 << 0), /* Real Time Counter overflow */
	EVSYS_ASYNCCH2_RTC_CMP_gc      = (0x09 << 0), /* Real Time Counter compare */
	EVSYS_ASYNCCH2_PORTC_PIN0_gc   = (0x0A << 0), /* Asynchronous Event from Pin PC0 */
	EVSYS_ASYNCCH2_PORTC_PIN1_gc   = (0x0B << 0), /* Asynchronous Event from Pin PC1 */
	EVSYS_ASYNCCH2_PORTC_PIN2_gc   = (0x0C << 0), /* Asynchronous Event from Pin PC2 */
	EVSYS_ASYNCCH2_PORTC_PIN3_gc   = (0x0D << 0), /* Asynchronous Event from Pin PC3 */
	EVSYS_ASYNCCH2_PORTC_PIN4_gc   = (0x0E << 0), /* Asynchronous Event from Pin PC4 */
	EVSYS_ASYNCCH2_PORTC_PIN5_gc   = (0x0F << 0), /* Asynchronous Event from Pin PC5 */
	EVSYS_ASYNCCH2_AC1_OUT_gc      = (0x10 << 0), /* Analog Comparator 1 out */
	EVSYS_ASYNCCH2_AC2_OUT_gc      = (0x11 << 0), /* Analog Comparator 2 out */
} EVSYS_ASYNCCH2_t;

/* Asynchronous Channel 3 Generator Selection select */
typedef enum EVSYS_ASYNCCH3_enum {
	EVSYS_ASYNCCH3_OFF_gc          = (0x00 << 0), /* Off */
	EVSYS_ASYNCCH3_CCL_LUT0_gc     = (0x01 << 0), /* Configurable custom logic LUT0 */
	EVSYS_ASYNCCH3_CCL_LUT1_gc     = (0x02 << 0), /* Configurable custom logic LUT1 */
	EVSYS_ASYNCCH3_AC0_OUT_gc      = (0x03 << 0), /* Analog Comparator 0 out */
	EVSYS_ASYNCCH3_TCD0_CMPBCLR_gc = (0x04 << 0), /* Timer/Counter type D compare B clear */
	EVSYS_ASYNCCH3_TCD0_CMPASET_gc = (0x05 << 0), /* Timer/Counter type D compare A set */
	EVSYS_ASYNCCH3_TCD0_CMPBSET_gc = (0x06 << 0), /* Timer/Counter type D compare B set */
	EVSYS_ASYNCCH3_TCD0_PROGEV_gc  = (0x07 << 0), /* Timer/Counter type D program event */
	EVSYS_ASYNCCH3_RTC_OVF_gc      = (0x08 << 0), /* Real Time Counter overflow */
	EVSYS_ASYNCCH3_RTC_CMP_gc      = (0x09 << 0), /* Real Time Counter compare */
	EVSYS_ASYNCCH3_PIT_DIV8192_gc  = (0x0A << 0), /* Periodic Interrupt CLK_RTC div 8192 */
	EVSYS_ASYNCCH3_PIT_DIV4096_gc  = (0x0B << 0), /* Periodic Interrupt CLK_RTC div 4096 */
	EVSYS_ASYNCCH3_PIT_DIV2048_gc  = (0x0C << 0), /* Periodic Interrupt CLK_RTC div 2048 */
	EVSYS_ASYNCCH3_PIT_DIV1024_gc  = (0x0D << 0), /* Periodic Interrupt CLK_RTC div 1024 */
	EVSYS_ASYNCCH3_PIT_DIV512_gc   = (0x0E << 0), /* Periodic Interrupt CLK_RTC div 512 */
	EVSYS_ASYNCCH3_PIT_DIV256_gc   = (0x0F << 0), /* Periodic Interrupt CLK_RTC div 256 */
	EVSYS_ASYNCCH3_PIT_DIV128_gc   = (0x10 << 0), /* Periodic Interrupt CLK_RTC div 128 */
	EVSYS_ASYNCCH3_PIT_DIV64_gc    = (0x11 << 0), /* Periodic Interrupt CLK_RTC div 64 */
	EVSYS_ASYNCCH3_AC1_OUT_gc      = (0x12 << 0), /* Analog Comparator 1 out */
	EVSYS_ASYNCCH3_AC2_OUT_gc      = (0x13 << 0), /* Analog Comparator 2 out */
} EVSYS_ASYNCCH3_t;

/* Asynchronous User Ch 0 Input Selection - TCB0 select */
typedef enum EVSYS_ASYNCUSER0_enum {
	EVSYS_ASYNCUSER0_OFF_gc      = (0x00 << 0), /* Off */
	EVSYS_ASYNCUSER0_SYNCCH0_gc  = (0x01 << 0), /* Synchronous Event Channel 0 */
	EVSYS_ASYNCUSER0_SYNCCH1_gc  = (0x02 << 0), /* Synchronous Event Channel 1 */
	EVSYS_ASYNCUSER0_ASYNCCH0_gc = (0x03 << 0), /* Asynchronous Event Channel 0 */
	EVSYS_ASYNCUSER0_ASYNCCH1_gc = (0x04 << 0), /* Asynchronous Event Channel 1 */
	EVSYS_ASYNCUSER0_ASYNCCH2_gc = (0x05 << 0), /* Asynchronous Event Channel 2 */
	EVSYS_ASYNCUSER0_ASYNCCH3_gc = (0x06 << 0), /* Asynchronous Event Channel 3 */
} EVSYS_ASYNCUSER0_t;

/* Asynchronous User Ch 1 Input Selection - ADC0 select */
typedef enum EVSYS_ASYNCUSER1_enum {
	EVSYS_ASYNCUSER1_OFF_gc      = (0x00 << 0), /* Off */
	EVSYS_ASYNCUSER1_SYNCCH0_gc  = (0x01 << 0), /* Synchronous Event Channel 0 */
	EVSYS_ASYNCUSER1_SYNCCH1_gc  = (0x02 << 0), /* Synchronous Event Channel 1 */
	EVSYS_ASYNCUSER1_ASYNCCH0_gc = (0x03 << 0), /* Asynchronous Event Channel 0 */
	EVSYS_ASYNCUSER1_ASYNCCH1_gc = (0x04 << 0), /* Asynchronous Event Channel 1 */
	EVSYS_ASYNCUSER1_ASYNCCH2_gc = (0x05 << 0), /* Asynchronous Event Channel 2 */
	EVSYS_ASYNCUSER1_ASYNCCH3_gc = (0x06 << 0), /* Asynchronous Event Channel 3 */
} EVSYS_ASYNCUSER1_t;

/* Asynchronous User Ch 10 Input Selection - Event Out 2 select */
typedef enum EVSYS_ASYNCUSER10_enum {
	EVSYS_ASYNCUSER10_OFF_gc      = (0x00 << 0), /* Off */
	EVSYS_ASYNCUSER10_SYNCCH0_gc  = (0x01 << 0), /* Synchronous Event Channel 0 */
	EVSYS_ASYNCUSER10_SYNCCH1_gc  = (0x02 << 0), /* Synchronous Event Channel 1 */
	EVSYS_ASYNCUSER10_ASYNCCH0_gc = (0x03 << 0), /* Asynchronous Event Channel 0 */
	EVSYS_ASYNCUSER10_ASYNCCH1_gc = (0x04 << 0), /* Asynchronous Event Channel 1 */
	EVSYS_ASYNCUSER10_ASYNCCH2_gc = (0x05 << 0), /* Asynchronous Event Channel 2 */
	EVSYS_ASYNCUSER10_ASYNCCH3_gc = (0x06 << 0), /* Asynchronous Event Channel 3 */
} EVSYS_ASYNCUSER10_t;

/* Asynchronous User Ch 11 Input Selection - TCB1 select */
typedef enum EVSYS_ASYNCUSER11_enum {
	EVSYS_ASYNCUSER11_OFF_gc      = (0x00 << 0), /* Off */
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
	EVSYS_ASYNCUSER9_ASYNCCH1_gc = (0x04 << 0), /* Asynchronous Event Channel 1 */
	EVSYS_ASYNCUSER9_ASYNCCH2_gc = (0x05 << 0), /* Asynchronous Event Channel 2 */
	EVSYS_ASYNCUSER9_ASYNCCH3_gc = (0x06 << 0), /* Asynchronous Event Channel 3 */
} EVSYS_ASYNCUSER9_t;

/* Synchronous Channel 0 Generator Selection select */
typedef enum EVSYS_SYNCCH0_enum {
	EVSYS_SYNCCH0_OFF_gc           = (0x00 << 0), /* Off */
	EVSYS_SYNCCH0_TCB0_gc          = (0x01 << 0), /* Timer/Counter B0 */
	EVSYS_SYNCCH0_TCA0_OVF_LUNF_gc = (0x02 << 0), /* Timer/Counter A0 overflow */
	EVSYS_SYNCCH0_TCA0_HUNF_gc     = (0x03 << 0), /* Timer/Counter A0 underflow high byte (split mode) */
	EVSYS_SYNCCH0_TCA0_CMP0_gc     = (0x04 << 0), /* Timer/Counter A0 compare 0 */
	EVSYS_SYNCCH0_TCA0_CMP1_gc     = (0x05 << 0), /* Timer/Counter A0 compare 1 */
	EVSYS_SYNCCH0_TCA0_CMP2_gc     = (0x06 << 0), /* Timer/Counter A0 compare 2 */
	EVSYS_SYNCCH0_PORTC_PIN0_gc    = (0x07 << 0), /* Synchronous Event from Pin PC0 */
	EVSYS_SYNCCH0_PORTC_PIN1_gc    = (0x08 << 0), /* Synchronous Event from Pin PC1 */
	EVSYS_SYNCCH0_PORTC_PIN2_gc    = (0x09 << 0), /* Synchronous Event from Pin PC2 */
	EVSYS_SYNCCH0_PORTC_PIN3_gc    = (0x0A << 0), /* Synchronous Event from Pin PC3 */
	EVSYS_SYNCCH0_PORTC_PIN4_gc    = (0x0B << 0), /* Synchronous Event from Pin PC4 */
	EVSYS_SYNCCH0_PORTC_PIN5_gc    = (0x0C << 0), /* Synchronous Event from Pin PC5 */
	EVSYS_SYNCCH0_PORTA_PIN0_gc    = (0x0D << 0), /* Synchronous Event from Pin PA0 */
	EVSYS_SYNCCH0_PORTA_PIN1_gc    = (0x0E << 0), /* Synchronous Event from Pin PA1 */
	EVSYS_SYNCCH0_PORTA_PIN2_gc    = (0x0F << 0), /* Synchronous Event from Pin PA2 */
	EVSYS_SYNCCH0_PORTA_PIN3_gc    = (0x10 << 0), /* Synchronous Event from Pin PA3 */
	EVSYS_SYNCCH0_PORTA_PIN4_gc    = (0x11 << 0), /* Synchronous Event from Pin PA4 */
	EVSYS_SYNCCH0_PORTA_PIN5_gc    = (0x12 << 0), /* Synchronous Event from Pin PA5 */
	EVSYS_SYNCCH0_PORTA_PIN6_gc    = (0x13 << 0), /* Synchronous Event from Pin PA6 */
	EVSYS_SYNCCH0_PORTA_PIN7_gc    = (0x14 << 0), /* Synchronous Event from Pin PA7 */
	EVSYS_SYNCCH0_TCB1_gc          = (0x15 << 0), /* Timer/Counter B1 */
} EVSYS_SYNCCH0_t;

/* Synchronous Channel 1 Generator Selection select */
typedef enum EVSYS_SYNCCH1_enum {
	EVSYS_SYNCCH1_OFF_gc           = (0x00 << 0), /* Off */
	EVSYS_SYNCCH1_TCB0_gc          = (0x01 << 0), /* Timer/Counter B0 */
	EVSYS_SYNCCH1_TCA0_OVF_LUNF_gc = (0x02 << 0), /* Timer/Counter A0 overflow */
	EVSYS_SYNCCH1_TCA0_HUNF_gc     = (0x03 << 0), /* Timer/Counter A0 underflow high byte (split mode) */
	EVSYS_SYNCCH1_TCA0_CMP0_gc     = (0x04 << 0), /* Timer/Counter A0 compare 0 */
	EVSYS_SYNCCH1_TCA0_CMP1_gc     = (0x05 << 0), /* Timer/Counter A0 compare 1 */
	EVSYS_SYNCCH1_TCA0_CMP2_gc     = (0x06 << 0), /* Timer/Counter A0 compare 2 */
	EVSYS_SYNCCH1_PORTB_PIN0_gc    = (0x08 << 0), /* Synchronous Event from Pin PB0 */
	EVSYS_SYNCCH1_PORTB_PIN1_gc    = (0x09 << 0), /* Synchronous Event from Pin PB1 */
	EVSYS_SYNCCH1_PORTB_PIN2_gc    = (0x0A << 0), /* Synchronous Event from Pin PB2 */
	EVSYS_SYNCCH1_PORTB_PIN3_gc    = (0x0B << 0), /* Synchronous Event from Pin PB3 */
	EVSYS_SYNCCH1_PORTB_PIN4_gc    = (0x0C << 0), /* Synchronous Event from Pin PB4 */
	EVSYS_SYNCCH1_PORTB_PIN5_gc    = (0x0D << 0), /* Synchronous Event from Pin PB5 */
	EVSYS_SYNCCH1_PORTB_PIN6_gc    = (0x0E << 0), /* Synchronous Event from Pin PB6 */
	EVSYS_SYNCCH1_PORTB_PIN7_gc    = (0x0F << 0), /* Synchronous Event from Pin PB7 */
	EVSYS_SYNCCH1_TCB1_gc          = (0x10 << 0), /* Timer/Counter B1 */
} EVSYS_SYNCCH1_t;

/* Synchronous User Ch 0 - TCA0 select */
typedef enum EVSYS_SYNCUSER0_enum {
	EVSYS_SYNCUSER0_OFF_gc     = (0x00 << 0), /* Off */
	EVSYS_SYNCUSER0_SYNCCH0_gc = (0x01 << 0), /* Synchronous Event Channel 0 */
	EVSYS_SYNCUSER0_SYNCCH1_gc = (0x02 << 0), /* Synchronous Event Channel 1 */
} EVSYS_SYNCUSER0_t;

/* Synchronous User Ch 1 - USART0 select */
typedef enum EVSYS_SYNCUSER1_enum {
	EVSYS_SYNCUSER1_OFF_gc     = (0x00 << 0), /* Off */
	EVSYS_SYNCUSER1_SYNCCH0_gc = (0x01 << 0), /* Synchronous Event Channel 0 */
	EVSYS_SYNCUSER1_SYNCCH1_gc = (0x02 << 0), /* Synchronous Event Channel 1 */
} EVSYS_SYNCUSER1_t;

/*
--------------------------------------------------------------------------
FUSE - Fuses
--------------------------------------------------------------------------
*/

/* Fuses */
typedef struct FUSE_struct {
	register8_t WDTCFG; /* Watchdog Configuration */
	register8_t BODCFG; /* BOD Configuration */
	register8_t OSCCFG; /* Oscillator Configuration */
	register8_t reserved_1[1];
	register8_t TCD0CFG; /* TCD0 Configuration */
	register8_t SYSCFG0; /* System Configuration 0 */
	register8_t SYSCFG1; /* System Configuration 1 */
	register8_t APPEND;  /* Application Code Section End */
	register8_t BOOTEND; /* Boot Section End */
} FUSE_t;

/* avr-libc typedef for avr/fuse.h */
typedef FUSE_t NVM_FUSES_t;

/* BOD Operation in Active Mode select */
typedef enum ACTIVE_enum {
	ACTIVE_DIS_gc     = (0x00 << 2), /* Disabled */
	ACTIVE_ENABLED_gc = (0x01 << 2), /* Enabled */
	ACTIVE_SAMPLED_gc = (0x02 << 2), /* Sampled */
	ACTIVE_ENWAKE_gc  = (0x03 << 2), /* Enabled with wake-up halted until BOD is ready */
} ACTIVE_t;

/* CRC Source select */
typedef enum CRCSRC_enum {
	CRCSRC_FLASH_gc
	= (0x00 << 6), /* The CRC is performed on the entire Flash (boot, application code and application data section). */
	CRCSRC_BOOT_gc    = (0x01 << 6), /* The CRC is performed on the boot section of Flash */
	CRCSRC_BOOTAPP_gc = (0x02 << 6), /* The CRC is performed on the boot and application code section of Flash */
	CRCSRC_NOCRC_gc   = (0x03 << 6), /* Disable CRC. */
} CRCSRC_t;

/* Frequency Select select */
typedef enum FREQSEL_enum {
	FREQSEL_16MHZ_gc = (0x01 << 0), /* 16 MHz */
	FREQSEL_20MHZ_gc = (0x02 << 0), /* 20 MHz */
} FREQSEL_t;

/* BOD Level select */
typedef enum LVL_enum {
	LVL_BODLEVEL0_gc = (0x00 << 5), /* 1.8 V */
	LVL_BODLEVEL2_gc = (0x02 << 5), /* 2.6 V */
	LVL_BODLEVEL7_gc = (0x07 << 5), /* 4.2 V */
} LVL_t;

/* Watchdog Timeout Period select */
typedef enum PERIOD_enum {
	PERIOD_OFF_gc    = (0x00 << 0), /* Off */
	PERIOD_8CLK_gc   = (0x01 << 0), /* 8 cycles (8ms) */
	PERIOD_16CLK_gc  = (0x02 << 0), /* 16 cycles (16ms) */
	PERIOD_32CLK_gc  = (0x03 << 0), /* 32 cycles (32ms) */
	PERIOD_64CLK_gc  = (0x04 << 0), /* 64 cycles (64ms) */
	PERIOD_128CLK_gc = (0x05 << 0), /* 128 cycles (0.128s) */
	PERIOD_256CLK_gc = (0x06 << 0), /* 256 cycles (0.256s) */
	PERIOD_512CLK_gc = (0x07 << 0), /* 512 cycles (0.512s) */
	PERIOD_1KCLK_gc  = (0x08 << 0), /* 1K cycles (1.0s) */
	PERIOD_2KCLK_gc  = (0x09 << 0), /* 2K cycles (2.0s) */
	PERIOD_4KCLK_gc  = (0x0A << 0), /* 4K cycles (4.1s) */
	PERIOD_8KCLK_gc  = (0x0B << 0), /* 8K cycles (8.2s) */
} PERIOD_t;

/* Reset Pin Configuration select */
typedef enum RSTPINCFG_enum {
	RSTPINCFG_GPIO_gc = (0x00 << 2), /* GPIO mode */
	RSTPINCFG_UPDI_gc = (0x01 << 2), /* UPDI mode */
	RSTPINCFG_RST_gc  = (0x02 << 2), /* Reset mode */
} RSTPINCFG_t;

/* BOD Sample Frequency select */
typedef enum SAMPFREQ_enum {
	SAMPFREQ_1KHZ_gc  = (0x00 << 4), /* 1kHz sampling frequency */
	SAMPFREQ_125HZ_gc = (0x01 << 4), /* 125Hz sampling frequency */
} SAMPFREQ_t;

/* BOD Operation in Sleep Mode select */
typedef enum SLEEP_enum {
	SLEEP_DIS_gc     = (0x00 << 0), /* Disabled */
	SLEEP_ENABLED_gc = (0x01 << 0), /* Enabled */
	SLEEP_SAMPLED_gc = (0x02 << 0), /* Sampled */
} SLEEP_t;

/* Startup Time select */
typedef enum SUT_enum {
	SUT_0MS_gc  = (0x00 << 0), /* 0 ms */
	SUT_1MS_gc  = (0x01 << 0), /* 1 ms */
	SUT_2MS_gc  = (0x02 << 0), /* 2 ms */
	SUT_4MS_gc  = (0x03 << 0), /* 4 ms */
	SUT_8MS_gc  = (0x04 << 0), /* 8 ms */
	SUT_16MS_gc = (0x05 << 0), /* 16 ms */
	SUT_32MS_gc = (0x06 << 0), /* 32 ms */
	SUT_64MS_gc = (0x07 << 0), /* 64 ms */
} SUT_t;

/* Watchdog Window Timeout Period select */
typedef enum WINDOW_enum {
	WINDOW_OFF_gc    = (0x00 << 4), /* Off */
	WINDOW_8CLK_gc   = (0x01 << 4), /* 8 cycles (8ms) */
	WINDOW_16CLK_gc  = (0x02 << 4), /* 16 cycles (16ms) */
	WINDOW_32CLK_gc  = (0x03 << 4), /* 32 cycles (32ms) */
	WINDOW_64CLK_gc  = (0x04 << 4), /* 64 cycles (64ms) */
	WINDOW_128CLK_gc = (0x05 << 4), /* 128 cycles (0.128s) */
	WINDOW_256CLK_gc = (0x06 << 4), /* 256 cycles (0.256s) */
	WINDOW_512CLK_gc = (0x07 << 4), /* 512 cycles (0.512s) */
	WINDOW_1KCLK_gc  = (0x08 << 4), /* 1K cycles (1.0s) */
	WINDOW_2KCLK_gc  = (0x09 << 4), /* 2K cycles (2.0s) */
	WINDOW_4KCLK_gc  = (0x0A << 4), /* 4K cycles (4.1s) */
	WINDOW_8KCLK_gc  = (0x0B << 4), /* 8K cycles (8.2s) */
} WINDOW_t;

/*
--------------------------------------------------------------------------
LOCKBIT - Lockbit
--------------------------------------------------------------------------
*/

/* Lockbit */
typedef struct LOCKBIT_struct {
	register8_t LOCKBIT; /* Lock bits */
} LOCKBIT_t;

/* Lock Bits select */
typedef enum LB_enum {
	LB_RWLOCK_gc = (0x3A << 0), /* Read and write lock */
	LB_NOLOCK_gc = (0xC5 << 0), /* No locks */
} LB_t;

/*
--------------------------------------------------------------------------
NVMCTRL - Non-volatile Memory Controller
--------------------------------------------------------------------------
*/

/* Non-volatile Memory Controller */
typedef struct NVMCTRL_struct {
	register8_t CTRLA;    /* Control A */
	register8_t CTRLB;    /* Control B */
	register8_t STATUS;   /* Status */
	register8_t INTCTRL;  /* Interrupt Control */
	register8_t INTFLAGS; /* Interrupt Flags */
	register8_t reserved_1[1];
	_WORDREGISTER(DATA); /* Data */
	_WORDREGISTER(ADDR); /* Address */
	register8_t reserved_2[6];
} NVMCTRL_t;

/* Command select */
typedef enum NVMCTRL_CMD_enum {
	NVMCTRL_CMD_NONE_gc           = (0x00 << 0), /* No Command */
	NVMCTRL_CMD_PAGEWRITE_gc      = (0x01 << 0), /* Write page */
	NVMCTRL_CMD_PAGEERASE_gc      = (0x02 << 0), /* Erase page */
	NVMCTRL_CMD_PAGEERASEWRITE_gc = (0x03 << 0), /* Erase and write page */
	NVMCTRL_CMD_PAGEBUFCLR_gc     = (0x04 << 0), /* Page buffer clear */
	NVMCTRL_CMD_CHIPERASE_gc      = (0x05 << 0), /* Chip erase */
	NVMCTRL_CMD_EEERASE_gc        = (0x06 << 0), /* EEPROM erase */
	NVMCTRL_CMD_FUSEWRITE_gc      = (0x07 << 0), /* Write fuse (PDI only) */
} NVMCTRL_CMD_t;

/*
--------------------------------------------------------------------------
PORT - I/O Ports
--------------------------------------------------------------------------
*/

/* I/O Ports */
typedef struct PORT_struct {
	register8_t DIR;      /* Data Direction */
	register8_t DIRSET;   /* Data Direction Set */
	register8_t DIRCLR;   /* Data Direction Clear */
	register8_t DIRTGL;   /* Data Direction Toggle */
	register8_t OUT;      /* Output Value */
	register8_t OUTSET;   /* Output Value Set */
	register8_t OUTCLR;   /* Output Value Clear */
	register8_t OUTTGL;   /* Output Value Toggle */
	register8_t IN;       /* Input Value */
	register8_t INTFLAGS; /* Interrupt Flags */
	register8_t reserved_1[6];
	register8_t PIN0CTRL; /* Pin 0 Control */
	register8_t PIN1CTRL; /* Pin 1 Control */
	register8_t PIN2CTRL; /* Pin 2 Control */
	register8_t PIN3CTRL; /* Pin 3 Control */
	register8_t PIN4CTRL; /* Pin 4 Control */
	register8_t PIN5CTRL; /* Pin 5 Control */
	register8_t PIN6CTRL; /* Pin 6 Control */
	register8_t PIN7CTRL; /* Pin 7 Control */
	register8_t reserved_2[8];
} PORT_t;

/* Input/Sense Configuration select */
typedef enum PORT_ISC_enum {
	PORT_ISC_INTDISABLE_gc    = (0x00 << 0), /* Interrupt disabled but input buffer enabled */
	PORT_ISC_BOTHEDGES_gc     = (0x01 << 0), /* Sense Both Edges */
	PORT_ISC_RISING_gc        = (0x02 << 0), /* Sense Rising Edge */
	PORT_ISC_FALLING_gc       = (0x03 << 0), /* Sense Falling Edge */
	PORT_ISC_INPUT_DISABLE_gc = (0x04 << 0), /* Digital Input Buffer disabled */
	PORT_ISC_LEVEL_gc         = (0x05 << 0), /* Sense low Level */
} PORT_ISC_t;

/*
--------------------------------------------------------------------------
PORTMUX - Port Multiplexer
--------------------------------------------------------------------------
*/

/* Port Multiplexer */
typedef struct PORTMUX_struct {
	register8_t CTRLA; /* Port Multiplexer Control A */
	register8_t CTRLB; /* Port Multiplexer Control B */
	register8_t CTRLC; /* Port Multiplexer Control C */
	register8_t CTRLD; /* Port Multiplexer Control D */
	register8_t reserved_1[12];
} PORTMUX_t;

/* Configurable Custom Logic LUT0 select */
typedef enum PORTMUX_LUT0_enum {
	PORTMUX_LUT0_DEFAULT_gc   = (0x00 << 4), /* Default pin */
	PORTMUX_LUT0_ALTERNATE_gc = (0x01 << 4), /* Alternate pin */
} PORTMUX_LUT0_t;

/* Configurable Custom Logic LUT1 select */
typedef enum PORTMUX_LUT1_enum {
	PORTMUX_LUT1_DEFAULT_gc   = (0x00 << 5), /* Default pin */
	PORTMUX_LUT1_ALTERNATE_gc = (0x01 << 5), /* Alternate pin */
} PORTMUX_LUT1_t;

/* Port Multiplexer SPI0 select */
typedef enum PORTMUX_SPI0_enum {
	PORTMUX_SPI0_DEFAULT_gc   = (0x00 << 2), /* Default pins */
	PORTMUX_SPI0_ALTERNATE_gc = (0x01 << 2), /* Alternate pins */
} PORTMUX_SPI0_t;

/* Port Multiplexer TCA0 Output 0 select */
typedef enum PORTMUX_TCA00_enum {
	PORTMUX_TCA00_DEFAULT_gc   = (0x00 << 0), /* Default pin */
	PORTMUX_TCA00_ALTERNATE_gc = (0x01 << 0), /* Alternate pin */
} PORTMUX_TCA00_t;

/* Port Multiplexer TCA0 Output 1 select */
typedef enum PORTMUX_TCA01_enum {
	PORTMUX_TCA01_DEFAULT_gc   = (0x00 << 1), /* Default pin */
	PORTMUX_TCA01_ALTERNATE_gc = (0x01 << 1), /* Alternate pin */
} PORTMUX_TCA01_t;

/* Port Multiplexer TCA0 Output 2 select */
typedef enum PORTMUX_TCA02_enum {
	PORTMUX_TCA02_DEFAULT_gc   = (0x00 << 2), /* Default pin */
	PORTMUX_TCA02_ALTERNATE_gc = (0x01 << 2), /* Alternate pin */
} PORTMUX_TCA02_t;

/* Port Multiplexer TCA0 Output 3 select */
typedef enum PORTMUX_TCA03_enum {
	PORTMUX_TCA03_DEFAULT_gc   = (0x00 << 3), /* Default pin */
	PORTMUX_TCA03_ALTERNATE_gc = (0x01 << 3), /* Alternate pin */
} PORTMUX_TCA03_t;

/* Port Multiplexer TCA0 Output 4 select */
typedef enum PORTMUX_TCA04_enum {
	PORTMUX_TCA04_DEFAULT_gc   = (0x00 << 4), /* Default pin */
	PORTMUX_TCA04_ALTERNATE_gc = (0x01 << 4), /* Alternate pin */
} PORTMUX_TCA04_t;

/* Port Multiplexer TCA0 Output 5 select */
typedef enum PORTMUX_TCA05_enum {
	PORTMUX_TCA05_DEFAULT_gc   = (0x00 << 5), /* Default pin */
	PORTMUX_TCA05_ALTERNATE_gc = (0x01 << 5), /* Alternate pin */
} PORTMUX_TCA05_t;

/* Port Multiplexer TCB0 select */
typedef enum PORTMUX_TCB0_enum {
	PORTMUX_TCB0_DEFAULT_gc   = (0x00 << 0), /* Default pin */
	PORTMUX_TCB0_ALTERNATE_gc = (0x01 << 0), /* Alternate pin */
} PORTMUX_TCB0_t;

/* Port Multiplexer TCB1 select */
typedef enum PORTMUX_TCB1_enum {
	PORTMUX_TCB1_DEFAULT_gc   = (0x00 << 1), /* Default pin */
	PORTMUX_TCB1_ALTERNATE_gc = (0x01 << 1), /* Alternate pin */
} PORTMUX_TCB1_t;

/* Port Multiplexer TWI0 select */
typedef enum PORTMUX_TWI0_enum {
	PORTMUX_TWI0_DEFAULT_gc   = (0x00 << 4), /* Default pins */
	PORTMUX_TWI0_ALTERNATE_gc = (0x01 << 4), /* Alternate pins */
} PORTMUX_TWI0_t;

/* Port Multiplexer USART0 select */
typedef enum PORTMUX_USART0_enum {
	PORTMUX_USART0_DEFAULT_gc   = (0x00 << 0), /* Default pins */
	PORTMUX_USART0_ALTERNATE_gc = (0x01 << 0), /* Alternate pins */
} PORTMUX_USART0_t;

/*
--------------------------------------------------------------------------
RSTCTRL - Reset controller
--------------------------------------------------------------------------
*/

/* Reset controller */
typedef struct RSTCTRL_struct {
	register8_t RSTFR; /* Reset Flags */
	register8_t SWRR;  /* Software Reset */
	register8_t reserved_1[2];
} RSTCTRL_t;

/*
--------------------------------------------------------------------------
RTC - Real-Time Counter
--------------------------------------------------------------------------
*/

/* Real-Time Counter */
typedef struct RTC_struct {
	register8_t CTRLA;    /* Control A */
	register8_t STATUS;   /* Status */
	register8_t INTCTRL;  /* Interrupt Control */
	register8_t INTFLAGS; /* Interrupt Flags */
	register8_t TEMP;     /* Temporary */
	register8_t DBGCTRL;  /* Debug control */
	register8_t reserved_1[1];
	register8_t CLKSEL; /* Clock Select */
	_WORDREGISTER(CNT); /* Counter */
	_WORDREGISTER(PER); /* Period */
	_WORDREGISTER(CMP); /* Compare */
	register8_t reserved_2[2];
	register8_t PITCTRLA;    /* PIT Control A */
	register8_t PITSTATUS;   /* PIT Status */
	register8_t PITINTCTRL;  /* PIT Interrupt Control */
	register8_t PITINTFLAGS; /* PIT Interrupt Flags */
	register8_t reserved_3[1];
	register8_t PITDBGCTRL; /* PIT Debug control */
	register8_t reserved_4[10];
} RTC_t;

/* Clock Select select */
typedef enum RTC_CLKSEL_enum {
	RTC_CLKSEL_INT32K_gc  = (0x00 << 0), /* Internal 32kHz OSC */
	RTC_CLKSEL_INT1K_gc   = (0x01 << 0), /* Internal 1kHz OSC */
	RTC_CLKSEL_TOSC32K_gc = (0x02 << 0), /* 32KHz Crystal OSC */
	RTC_CLKSEL_EXTCLK_gc  = (0x03 << 0), /* External Clock */
} RTC_CLKSEL_t;

/* Period select */
typedef enum RTC_PERIOD_enum {
	RTC_PERIOD_OFF_gc      = (0x00 << 3), /* Off */
	RTC_PERIOD_CYC4_gc     = (0x01 << 3), /* RTC Clock Cycles 4 */
	RTC_PERIOD_CYC8_gc     = (0x02 << 3), /* RTC Clock Cycles 8 */
	RTC_PERIOD_CYC16_gc    = (0x03 << 3), /* RTC Clock Cycles 16 */
	RTC_PERIOD_CYC32_gc    = (0x04 << 3), /* RTC Clock Cycles 32 */
	RTC_PERIOD_CYC64_gc    = (0x05 << 3), /* RTC Clock Cycles 64 */
	RTC_PERIOD_CYC128_gc   = (0x06 << 3), /* RTC Clock Cycles 128 */
	RTC_PERIOD_CYC256_gc   = (0x07 << 3), /* RTC Clock Cycles 256 */
	RTC_PERIOD_CYC512_gc   = (0x08 << 3), /* RTC Clock Cycles 512 */
	RTC_PERIOD_CYC1024_gc  = (0x09 << 3), /* RTC Clock Cycles 1024 */
	RTC_PERIOD_CYC2048_gc  = (0x0A << 3), /* RTC Clock Cycles 2048 */
	RTC_PERIOD_CYC4096_gc  = (0x0B << 3), /* RTC Clock Cycles 4096 */
	RTC_PERIOD_CYC8192_gc  = (0x0C << 3), /* RTC Clock Cycles 8192 */
	RTC_PERIOD_CYC16384_gc = (0x0D << 3), /* RTC Clock Cycles 16384 */
	RTC_PERIOD_CYC32768_gc = (0x0E << 3), /* RTC Clock Cycles 32768 */
} RTC_PERIOD_t;

/* Prescaling Factor select */
typedef enum RTC_PRESCALER_enum {
	RTC_PRESCALER_DIV1_gc     = (0x00 << 3), /* RTC Clock / 1 */
	RTC_PRESCALER_DIV2_gc     = (0x01 << 3), /* RTC Clock / 2 */
	RTC_PRESCALER_DIV4_gc     = (0x02 << 3), /* RTC Clock / 4 */
	RTC_PRESCALER_DIV8_gc     = (0x03 << 3), /* RTC Clock / 8 */
	RTC_PRESCALER_DIV16_gc    = (0x04 << 3), /* RTC Clock / 16 */
	RTC_PRESCALER_DIV32_gc    = (0x05 << 3), /* RTC Clock / 32 */
	RTC_PRESCALER_DIV64_gc    = (0x06 << 3), /* RTC Clock / 64 */
	RTC_PRESCALER_DIV128_gc   = (0x07 << 3), /* RTC Clock / 128 */
	RTC_PRESCALER_DIV256_gc   = (0x08 << 3), /* RTC Clock / 256 */
	RTC_PRESCALER_DIV512_gc   = (0x09 << 3), /* RTC Clock / 512 */
	RTC_PRESCALER_DIV1024_gc  = (0x0A << 3), /* RTC Clock / 1024 */
	RTC_PRESCALER_DIV2048_gc  = (0x0B << 3), /* RTC Clock / 2048 */
	RTC_PRESCALER_DIV4096_gc  = (0x0C << 3), /* RTC Clock / 4096 */
	RTC_PRESCALER_DIV8192_gc  = (0x0D << 3), /* RTC Clock / 8192 */
	RTC_PRESCALER_DIV16384_gc = (0x0E << 3), /* RTC Clock / 16384 */
	RTC_PRESCALER_DIV32768_gc = (0x0F << 3), /* RTC Clock / 32768 */
} RTC_PRESCALER_t;

/*
--------------------------------------------------------------------------
SIGROW - Signature row
--------------------------------------------------------------------------
*/

/* Signature row */
typedef struct SIGROW_struct {
	register8_t DEVICEID0; /* Device ID Byte 0 */
	register8_t DEVICEID1; /* Device ID Byte 1 */
	register8_t DEVICEID2; /* Device ID Byte 2 */
	register8_t SERNUM0;   /* Serial Number Byte 0 */
	register8_t SERNUM1;   /* Serial Number Byte 1 */
	register8_t SERNUM2;   /* Serial Number Byte 2 */
	register8_t SERNUM3;   /* Serial Number Byte 3 */
	register8_t SERNUM4;   /* Serial Number Byte 4 */
	register8_t SERNUM5;   /* Serial Number Byte 5 */
	register8_t SERNUM6;   /* Serial Number Byte 6 */
	register8_t SERNUM7;   /* Serial Number Byte 7 */
	register8_t SERNUM8;   /* Serial Number Byte 8 */
	register8_t SERNUM9;   /* Serial Number Byte 9 */
	register8_t reserved_1[19];
	register8_t TEMPSENSE0; /* Temperature Sensor Calibration Byte 0 */
	register8_t TEMPSENSE1; /* Temperature Sensor Calibration Byte 1 */
	register8_t OSC16ERR3V; /* OSC16 error at 3V */
	register8_t OSC16ERR5V; /* OSC16 error at 5V */
	register8_t OSC20ERR3V; /* OSC20 error at 3V */
	register8_t OSC20ERR5V; /* OSC20 error at 5V */
	register8_t reserved_2[26];
} SIGROW_t;

/*
--------------------------------------------------------------------------
SLPCTRL - Sleep Controller
--------------------------------------------------------------------------
*/

/* Sleep Controller */
typedef struct SLPCTRL_struct {
	register8_t CTRLA; /* Control */
	register8_t reserved_1[1];
} SLPCTRL_t;

/* Sleep mode select */
typedef enum SLPCTRL_SMODE_enum {
	SLPCTRL_SMODE_IDLE_gc  = (0x00 << 1), /* Idle mode */
	SLPCTRL_SMODE_STDBY_gc = (0x01 << 1), /* Standby Mode */
	SLPCTRL_SMODE_PDOWN_gc = (0x02 << 1), /* Power-down Mode */
} SLPCTRL_SMODE_t;

#define SLEEP_MODE_IDLE (0x00 << 1)
#define SLEEP_MODE_STANDBY (0x01 << 1)
#define SLEEP_MODE_PWR_DOWN (0x02 << 1)
/*
--------------------------------------------------------------------------
SPI - Serial Peripheral Interface
--------------------------------------------------------------------------
*/

/* Serial Peripheral Interface */
typedef struct SPI_struct {
	register8_t CTRLA;    /* Control A */
	register8_t CTRLB;    /* Control B */
	register8_t INTCTRL;  /* Interrupt Control */
	register8_t INTFLAGS; /* Interrupt Flags */
	register8_t DATA;     /* Data */
	register8_t reserved_1[3];
} SPI_t;

/* SPI Mode select */
typedef enum SPI_MODE_enum {
	SPI_MODE_0_gc = (0x00 << 0), /* SPI Mode 0 */
	SPI_MODE_1_gc = (0x01 << 0), /* SPI Mode 1 */
	SPI_MODE_2_gc = (0x02 << 0), /* SPI Mode 2 */
	SPI_MODE_3_gc = (0x03 << 0), /* SPI Mode 3 */
} SPI_MODE_t;

/* Prescaler select */
typedef enum SPI_PRESC_enum {
	SPI_PRESC_DIV4_gc   = (0x00 << 1), /* System Clock / 4 */
	SPI_PRESC_DIV16_gc  = (0x01 << 1), /* System Clock / 16 */
	SPI_PRESC_DIV64_gc  = (0x02 << 1), /* System Clock / 64 */
	SPI_PRESC_DIV128_gc = (0x03 << 1), /* System Clock / 128 */
} SPI_PRESC_t;

/*
--------------------------------------------------------------------------
SYSCFG - System Configuration Registers
--------------------------------------------------------------------------
*/

/* System Configuration Registers */
typedef struct SYSCFG_struct {
	register8_t reserved_1[1];
	register8_t REVID;  /* Revision ID */
	register8_t EXTBRK; /* External Break */
	register8_t reserved_2[29];
} SYSCFG_t;

/*
--------------------------------------------------------------------------
TCA - 16-bit Timer/Counter Type A
--------------------------------------------------------------------------
*/

/* 16-bit Timer/Counter Type A - Single Mode */
typedef struct TCA_SINGLE_struct {
	register8_t CTRLA;    /* Control A */
	register8_t CTRLB;    /* Control B */
	register8_t CTRLC;    /* Control C */
	register8_t CTRLD;    /* Control D */
	register8_t CTRLECLR; /* Control E Clear */
	register8_t CTRLESET; /* Control E Set */
	register8_t CTRLFCLR; /* Control F Clear */
	register8_t CTRLFSET; /* Control F Set */
	register8_t reserved_1[1];
	register8_t EVCTRL;   /* Event Control */
	register8_t INTCTRL;  /* Interrupt Control */
	register8_t INTFLAGS; /* Interrupt Flags */
	register8_t reserved_2[2];
	register8_t DBGCTRL; /* Degbug Control */
	register8_t TEMP;    /* Temporary data for 16-bit Access */
	register8_t reserved_3[16];
	_WORDREGISTER(CNT); /* Count */
	register8_t reserved_4[4];
	_WORDREGISTER(PER);  /* Period */
	_WORDREGISTER(CMP0); /* Compare 0 */
	_WORDREGISTER(CMP1); /* Compare 1 */
	_WORDREGISTER(CMP2); /* Compare 2 */
	register8_t reserved_5[8];
	_WORDREGISTER(PERBUF);  /* Period Buffer */
	_WORDREGISTER(CMP0BUF); /* Compare 0 Buffer */
	_WORDREGISTER(CMP1BUF); /* Compare 1 Buffer */
	_WORDREGISTER(CMP2BUF); /* Compare 2 Buffer */
	register8_t reserved_6[2];
} TCA_SINGLE_t;

/* 16-bit Timer/Counter Type A - Split Mode */
typedef struct TCA_SPLIT_struct {
	register8_t CTRLA;    /* Control A */
	register8_t CTRLB;    /* Control B */
	register8_t CTRLC;    /* Control C */
	register8_t CTRLD;    /* Control D */
	register8_t CTRLECLR; /* Control E Clear */
	register8_t CTRLESET; /* Control E Set */
	register8_t reserved_1[4];
	register8_t INTCTRL;  /* Interrupt Control */
	register8_t INTFLAGS; /* Interrupt Flags */
	register8_t reserved_2[2];
	register8_t DBGCTRL; /* Degbug Control */
	register8_t reserved_3[17];
	register8_t LCNT; /* Low Count */
	register8_t HCNT; /* High Count */
	register8_t reserved_4[4];
	register8_t LPER;  /* Low Period */
	register8_t HPER;  /* High Period */
	register8_t LCMP0; /* Low Compare */
	register8_t HCMP0; /* High Compare */
	register8_t LCMP1; /* Low Compare */
	register8_t HCMP1; /* High Compare */
	register8_t LCMP2; /* Low Compare */
	register8_t HCMP2; /* High Compare */
	register8_t reserved_5[18];
} TCA_SPLIT_t;

/* 16-bit Timer/Counter Type A */
typedef union TCA_union {
	TCA_SINGLE_t SINGLE; /* 16-bit Timer/Counter Type A - Single Mode */
	TCA_SPLIT_t  SPLIT;  /* 16-bit Timer/Counter Type A - Split Mode */
} TCA_t;

/* Clock Selection select */
typedef enum TCA_SINGLE_CLKSEL_enum {
	TCA_SINGLE_CLKSEL_DIV1_gc    = (0x00 << 1), /* System Clock */
	TCA_SINGLE_CLKSEL_DIV2_gc    = (0x01 << 1), /* System Clock / 2 */
	TCA_SINGLE_CLKSEL_DIV4_gc    = (0x02 << 1), /* System Clock / 4 */
	TCA_SINGLE_CLKSEL_DIV8_gc    = (0x03 << 1), /* System Clock / 8 */
	TCA_SINGLE_CLKSEL_DIV16_gc   = (0x04 << 1), /* System Clock / 16 */
	TCA_SINGLE_CLKSEL_DIV64_gc   = (0x05 << 1), /* System Clock / 64 */
	TCA_SINGLE_CLKSEL_DIV256_gc  = (0x06 << 1), /* System Clock / 256 */
	TCA_SINGLE_CLKSEL_DIV1024_gc = (0x07 << 1), /* System Clock / 1024 */
} TCA_SINGLE_CLKSEL_t;

/* Command select */
typedef enum TCA_SINGLE_CMD_enum {
	TCA_SINGLE_CMD_NONE_gc    = (0x00 << 2), /* No Command */
	TCA_SINGLE_CMD_UPDATE_gc  = (0x01 << 2), /* Force Update */
	TCA_SINGLE_CMD_RESTART_gc = (0x02 << 2), /* Force Restart */
	TCA_SINGLE_CMD_RESET_gc   = (0x03 << 2), /* Force Hard Reset */
} TCA_SINGLE_CMD_t;

/* Direction select */
typedef enum TCA_SINGLE_DIR_enum {
	TCA_SINGLE_DIR_UP_gc   = (0x00 << 0), /* Count up */
	TCA_SINGLE_DIR_DOWN_gc = (0x01 << 0), /* Count down */
} TCA_SINGLE_DIR_t;

/* Event Action select */
typedef enum TCA_SINGLE_EVACT_enum {
	TCA_SINGLE_EVACT_POSEDGE_gc = (0x00 << 1), /* Count on positive edge event */
	TCA_SINGLE_EVACT_ANYEDGE_gc = (0x01 << 1), /* Count on any edge event */
	TCA_SINGLE_EVACT_HIGHLVL_gc = (0x02 << 1), /* Count on prescaled clock while event line is 1. */
	TCA_SINGLE_EVACT_UPDOWN_gc
	= (0x03 << 1), /* Count on prescaled clock. Event controls count direction. Up-count when event line is 0,
	                  down-count when event line is 1. */
} TCA_SINGLE_EVACT_t;

/* Waveform generation mode select */
typedef enum TCA_SINGLE_WGMODE_enum {
	TCA_SINGLE_WGMODE_NORMAL_gc      = (0x00 << 0), /* Normal Mode */
	TCA_SINGLE_WGMODE_FRQ_gc         = (0x01 << 0), /* Frequency Generation Mode */
	TCA_SINGLE_WGMODE_SINGLESLOPE_gc = (0x03 << 0), /* Single Slope PWM */
	TCA_SINGLE_WGMODE_DSTOP_gc       = (0x05 << 0), /* Dual Slope PWM, overflow on TOP */
	TCA_SINGLE_WGMODE_DSBOTH_gc      = (0x06 << 0), /* Dual Slope PWM, overflow on TOP and BOTTOM */
	TCA_SINGLE_WGMODE_DSBOTTOM_gc    = (0x07 << 0), /* Dual Slope PWM, overflow on BOTTOM */
} TCA_SINGLE_WGMODE_t;

/* Clock Selection select */
typedef enum TCA_SPLIT_CLKSEL_enum {
	TCA_SPLIT_CLKSEL_DIV1_gc    = (0x00 << 1), /* System Clock */
	TCA_SPLIT_CLKSEL_DIV2_gc    = (0x01 << 1), /* System Clock / 2 */
	TCA_SPLIT_CLKSEL_DIV4_gc    = (0x02 << 1), /* System Clock / 4 */
	TCA_SPLIT_CLKSEL_DIV8_gc    = (0x03 << 1), /* System Clock / 8 */
	TCA_SPLIT_CLKSEL_DIV16_gc   = (0x04 << 1), /* System Clock / 16 */
	TCA_SPLIT_CLKSEL_DIV64_gc   = (0x05 << 1), /* System Clock / 64 */
	TCA_SPLIT_CLKSEL_DIV256_gc  = (0x06 << 1), /* System Clock / 256 */
	TCA_SPLIT_CLKSEL_DIV1024_gc = (0x07 << 1), /* System Clock / 1024 */
} TCA_SPLIT_CLKSEL_t;

/* Command select */
typedef enum TCA_SPLIT_CMD_enum {
	TCA_SPLIT_CMD_NONE_gc    = (0x00 << 2), /* No Command */
	TCA_SPLIT_CMD_UPDATE_gc  = (0x01 << 2), /* Force Update */
	TCA_SPLIT_CMD_RESTART_gc = (0x02 << 2), /* Force Restart */
	TCA_SPLIT_CMD_RESET_gc   = (0x03 << 2), /* Force Hard Reset */
} TCA_SPLIT_CMD_t;

/*
--------------------------------------------------------------------------
TCB - 16-bit Timer Type B
--------------------------------------------------------------------------
*/

/* 16-bit Timer Type B */
typedef struct TCB_struct {
	register8_t CTRLA; /* Control A */
	register8_t CTRLB; /* Control Register B */
	register8_t reserved_1[2];
	register8_t EVCTRL;   /* Event Control */
	register8_t INTCTRL;  /* Interrupt Control */
	register8_t INTFLAGS; /* Interrupt Flags */
	register8_t STATUS;   /* Status */
	register8_t DBGCTRL;  /* Debug Control */
	register8_t TEMP;     /* Temporary Value */
	_WORDREGISTER(CNT);   /* Count */
	_WORDREGISTER(CCMP);  /* Compare or Capture */
	register8_t reserved_2[2];
} TCB_t;

/* Clock Select select */
typedef enum TCB_CLKSEL_enum {
	TCB_CLKSEL_CLKDIV1_gc = (0x00 << 1), /* CLK_PER (No Prescaling) */
	TCB_CLKSEL_CLKDIV2_gc = (0x01 << 1), /* CLK_PER/2 (From Prescaler) */
	TCB_CLKSEL_CLKTCA_gc  = (0x02 << 1), /* Use Clock from TCA */
} TCB_CLKSEL_t;

/* Timer Mode select */
typedef enum TCB_CNTMODE_enum {
	TCB_CNTMODE_INT_gc     = (0x00 << 0), /* Periodic Interrupt */
	TCB_CNTMODE_TIMEOUT_gc = (0x01 << 0), /* Periodic Timeout */
	TCB_CNTMODE_CAPT_gc    = (0x02 << 0), /* Input Capture Event */
	TCB_CNTMODE_FRQ_gc     = (0x03 << 0), /* Input Capture Frequency measurement */
	TCB_CNTMODE_PW_gc      = (0x04 << 0), /* Input Capture Pulse-Width measurement */
	TCB_CNTMODE_FRQPW_gc   = (0x05 << 0), /* Input Capture Frequency and Pulse-Width measurement */
	TCB_CNTMODE_SINGLE_gc  = (0x06 << 0), /* Single Shot */
	TCB_CNTMODE_PWM8_gc    = (0x07 << 0), /* 8-bit PWM */
} TCB_CNTMODE_t;

/*
--------------------------------------------------------------------------
TCD - Timer Counter D
--------------------------------------------------------------------------
*/

/* Timer Counter D */
typedef struct TCD_struct {
	register8_t CTRLA; /* Control A */
	register8_t CTRLB; /* Control B */
	register8_t CTRLC; /* Control C */
	register8_t CTRLD; /* Control D */
	register8_t CTRLE; /* Control E */
	register8_t reserved_1[3];
	register8_t EVCTRLA; /* EVCTRLA */
	register8_t EVCTRLB; /* EVCTRLB */
	register8_t reserved_2[2];
	register8_t INTCTRL;  /* Interrupt Control */
	register8_t INTFLAGS; /* Interrupt Flags */
	register8_t STATUS;   /* Status */
	register8_t reserved_3[1];
	register8_t INPUTCTRLA; /* Input Control A */
	register8_t INPUTCTRLB; /* Input Control B */
	register8_t FAULTCTRL;  /* Fault Control */
	register8_t reserved_4[1];
	register8_t DLYCTRL; /* Delay Control */
	register8_t DLYVAL;  /* Delay value */
	register8_t reserved_5[2];
	register8_t DITCTRL; /* Dither Control A */
	register8_t DITVAL;  /* Dither value */
	register8_t reserved_6[4];
	register8_t DBGCTRL; /* Debug Control */
	register8_t reserved_7[3];
	_WORDREGISTER(CAPTUREA); /* Capture A */
	_WORDREGISTER(CAPTUREB); /* Capture B */
	register8_t reserved_8[2];
	_WORDREGISTER(CMPASET); /* Compare A Set */
	_WORDREGISTER(CMPACLR); /* Compare A Clear */
	_WORDREGISTER(CMPBSET); /* Compare B Set */
	_WORDREGISTER(CMPBCLR); /* Compare B Clear */
	register8_t reserved_9[16];
} TCD_t;

/* event action select */
typedef enum TCD_ACTION_enum {
	TCD_ACTION_FAULT_gc   = (0x00 << 2), /* Event trigger a fault */
	TCD_ACTION_CAPTURE_gc = (0x01 << 2), /* Event trigger a fault and capture */
} TCD_ACTION_t;

/* event config select */
typedef enum TCD_CFG_enum {
	TCD_CFG_NEITHER_gc = (0x00 << 6), /* Neither Filter nor Asynchronous Event is enabled */
	TCD_CFG_FILTER_gc  = (0x01 << 6), /* Input Capture Noise Cancellation Filter enabled */
	TCD_CFG_ASYNC_gc   = (0x02 << 6), /* Asynchronous Event output qualification enabled */
} TCD_CFG_t;

/* clock select select */
typedef enum TCD_CLKSEL_enum {
	TCD_CLKSEL_20MHZ_gc  = (0x00 << 5), /* 20 MHz oscillator */
	TCD_CLKSEL_EXTCLK_gc = (0x02 << 5), /* External clock */
	TCD_CLKSEL_SYSCLK_gc = (0x03 << 5), /* System clock */
} TCD_CLKSEL_t;

/* Compare C output select select */
typedef enum TCD_CMPCSEL_enum {
	TCD_CMPCSEL_PWMA_gc = (0x00 << 6), /* PWM A output */
	TCD_CMPCSEL_PWMB_gc = (0x01 << 6), /* PWM B output */
} TCD_CMPCSEL_t;

/* Compare D output select select */
typedef enum TCD_CMPDSEL_enum {
	TCD_CMPDSEL_PWMA_gc = (0x00 << 7), /* PWM A output */
	TCD_CMPDSEL_PWMB_gc = (0x01 << 7), /* PWM B output */
} TCD_CMPDSEL_t;

/* counter prescaler select */
typedef enum TCD_CNTPRES_enum {
	TCD_CNTPRES_DIV1_gc  = (0x00 << 3), /* Sync clock divided by 1 */
	TCD_CNTPRES_DIV4_gc  = (0x01 << 3), /* Sync clock divided by 4 */
	TCD_CNTPRES_DIV32_gc = (0x02 << 3), /* Sync clock divided by 32 */
} TCD_CNTPRES_t;

/* dither select select */
typedef enum TCD_DITHERSEL_enum {
	TCD_DITHERSEL_ONTIMEB_gc    = (0x00 << 0), /* On-time ramp B */
	TCD_DITHERSEL_ONTIMEAB_gc   = (0x01 << 0), /* On-time ramp A and B */
	TCD_DITHERSEL_DEADTIMEB_gc  = (0x02 << 0), /* Dead-time rampB */
	TCD_DITHERSEL_DEADTIMEAB_gc = (0x03 << 0), /* Dead-time ramp A and B */
} TCD_DITHERSEL_t;

/* Delay prescaler select */
typedef enum TCD_DLYPRESC_enum {
	TCD_DLYPRESC_DIV1_gc = (0x00 << 4), /* No prescaling */
	TCD_DLYPRESC_DIV2_gc = (0x01 << 4), /* Prescale with 2 */
	TCD_DLYPRESC_DIV4_gc = (0x02 << 4), /* Prescale with 4 */
	TCD_DLYPRESC_DIV8_gc = (0x03 << 4), /* Prescale with 8 */
} TCD_DLYPRESC_t;

/* Delay select select */
typedef enum TCD_DLYSEL_enum {
	TCD_DLYSEL_OFF_gc     = (0x00 << 0), /* No delay */
	TCD_DLYSEL_INBLANK_gc = (0x01 << 0), /* Input blanking enabled */
	TCD_DLYSEL_EVENT_gc   = (0x02 << 0), /* Event delay enabled */
} TCD_DLYSEL_t;

/* Delay trigger select */
typedef enum TCD_DLYTRIG_enum {
	TCD_DLYTRIG_CMPASET_gc = (0x00 << 2), /* Compare A set */
	TCD_DLYTRIG_CMPACLR_gc = (0x01 << 2), /* Compare A clear */
	TCD_DLYTRIG_CMPBSET_gc = (0x02 << 2), /* Compare B set */
	TCD_DLYTRIG_CMPBCLR_gc = (0x03 << 2), /* Compare B clear */
} TCD_DLYTRIG_t;

/* edge select select */
typedef enum TCD_EDGE_enum {
	TCD_EDGE_FALL_LOW_gc = (0x00 << 4), /* The falling edge or low level of event generates retrigger or fault action */
	TCD_EDGE_RISE_HIGH_gc
	= (0x01 << 4), /* The rising edge or high level of event generates retrigger or fault action */
} TCD_EDGE_t;

/* Input mode select */
typedef enum TCD_INPUTMODE_enum {
	TCD_INPUTMODE_NONE_gc         = (0x00 << 0), /* Input has no actions */
	TCD_INPUTMODE_JMPWAIT_gc      = (0x01 << 0), /* Stop output, jump to opposite compare cycle and wait */
	TCD_INPUTMODE_EXECWAIT_gc     = (0x02 << 0), /* Stop output, execute opposite compare cycle and wait */
	TCD_INPUTMODE_EXECFAULT_gc    = (0x03 << 0), /* stop output, execute opposite compare cycle while fault active */
	TCD_INPUTMODE_FREQ_gc         = (0x04 << 0), /* Stop all outputs, maintain frequency */
	TCD_INPUTMODE_EXECDT_gc       = (0x05 << 0), /* Stop all outputs, execute dead time while fault active */
	TCD_INPUTMODE_WAIT_gc         = (0x06 << 0), /* Stop all outputs, jump to next compare cycle and wait */
	TCD_INPUTMODE_WAITSW_gc       = (0x07 << 0), /* Stop all outputs, wait for software action */
	TCD_INPUTMODE_EDGETRIG_gc     = (0x08 << 0), /* Stop output on edge, jump to next compare cycle */
	TCD_INPUTMODE_EDGETRIGFREQ_gc = (0x09 << 0), /* Stop output on edge, maintain frequency */
	TCD_INPUTMODE_LVLTRIGFREQ_gc  = (0x0A << 0), /* Stop output at level, maintain frequency */
} TCD_INPUTMODE_t;

/* Synchronization prescaler select */
typedef enum TCD_SYNCPRES_enum {
	TCD_SYNCPRES_DIV1_gc = (0x00 << 1), /* Selected clock source divided by 1 */
	TCD_SYNCPRES_DIV2_gc = (0x01 << 1), /* Selected clock source divided by 2 */
	TCD_SYNCPRES_DIV4_gc = (0x02 << 1), /* Selected clock source divided by 4 */
	TCD_SYNCPRES_DIV8_gc = (0x03 << 1), /* Selected clock source divided by 8 */
} TCD_SYNCPRES_t;

/* Waveform generation mode select */
typedef enum TCD_WGMODE_enum {
	TCD_WGMODE_ONERAMP_gc  = (0x00 << 0), /* One ramp mode */
	TCD_WGMODE_TWORAMP_gc  = (0x01 << 0), /* Two ramp mode */
	TCD_WGMODE_FOURRAMP_gc = (0x02 << 0), /* Four ramp mode */
	TCD_WGMODE_DS_gc       = (0x03 << 0), /* Dual slope mode */
} TCD_WGMODE_t;

/*
--------------------------------------------------------------------------
TWI - Two-Wire Interface
--------------------------------------------------------------------------
*/

/* Two-Wire Interface */
typedef struct TWI_struct {
	register8_t CTRLA; /* Control A */
	register8_t reserved_1[1];
	register8_t DBGCTRL;   /* Debug Control Register */
	register8_t MCTRLA;    /* Master Control A */
	register8_t MCTRLB;    /* Master Control B */
	register8_t MSTATUS;   /* Master Status */
	register8_t MBAUD;     /* Master Baurd Rate Control */
	register8_t MADDR;     /* Master Address */
	register8_t MDATA;     /* Master Data */
	register8_t SCTRLA;    /* Slave Control A */
	register8_t SCTRLB;    /* Slave Control B */
	register8_t SSTATUS;   /* Slave Status */
	register8_t SADDR;     /* Slave Address */
	register8_t SDATA;     /* Slave Data */
	register8_t SADDRMASK; /* Slave Address Mask */
	register8_t reserved_2[1];
} TWI_t;

/* Acknowledge Action select */
typedef enum TWI_ACKACT_enum {
	TWI_ACKACT_ACK_gc  = (0x00 << 2), /* Send ACK */
	TWI_ACKACT_NACK_gc = (0x01 << 2), /* Send NACK */
} TWI_ACKACT_t;

/* Slave Address or Stop select */
typedef enum TWI_AP_enum {
	TWI_AP_STOP_gc = (0x00 << 0), /* Stop condition generated APIF */
	TWI_AP_ADR_gc  = (0x01 << 0), /* Address detection generated APIF */
} TWI_AP_t;

/* Bus State select */
typedef enum TWI_BUSSTATE_enum {
	TWI_BUSSTATE_UNKNOWN_gc = (0x00 << 0), /* Unknown Bus State */
	TWI_BUSSTATE_IDLE_gc    = (0x01 << 0), /* Bus is Idle */
	TWI_BUSSTATE_OWNER_gc   = (0x02 << 0), /* This Module Controls The Bus */
	TWI_BUSSTATE_BUSY_gc    = (0x03 << 0), /* The Bus is Busy */
} TWI_BUSSTATE_t;

/* Command select */
typedef enum TWI_MCMD_enum {
	TWI_MCMD_NOACT_gc     = (0x00 << 0), /* No Action */
	TWI_MCMD_REPSTART_gc  = (0x01 << 0), /* Issue Repeated Start Condition */
	TWI_MCMD_RECVTRANS_gc = (0x02 << 0), /* Receive or Transmit Data, depending on DIR */
	TWI_MCMD_STOP_gc      = (0x03 << 0), /* Issue Stop Condition */
} TWI_MCMD_t;

/* Command select */
typedef enum TWI_SCMD_enum {
	TWI_SCMD_NOACT_gc     = (0x00 << 0), /* No Action */
	TWI_SCMD_COMPTRANS_gc = (0x02 << 0), /* Used To Complete a Transaction */
	TWI_SCMD_RESPONSE_gc  = (0x03 << 0), /* Used in Response to Address/Data Interrupt */
} TWI_SCMD_t;

/* SDA Hold Time select */
typedef enum TWI_SDAHOLD_enum {
	TWI_SDAHOLD_OFF_gc   = (0x00 << 2), /* SDA hold time off */
	TWI_SDAHOLD_50NS_gc  = (0x01 << 2), /* Typical 50ns hold time */
	TWI_SDAHOLD_300NS_gc = (0x02 << 2), /* Typical 300ns hold time */
	TWI_SDAHOLD_500NS_gc = (0x03 << 2), /* Typical 500ns hold time */
} TWI_SDAHOLD_t;

/* SDA Setup Time select */
typedef enum TWI_SDASETUP_enum {
	TWI_SDASETUP_4CYC_gc = (0x00 << 4), /* SDA setup time is 4 clock cycles */
	TWI_SDASETUP_8CYC_gc = (0x01 << 4), /* SDA setup time is 8 clock cycles */
} TWI_SDASETUP_t;

/* Inactive Bus Timeout select */
typedef enum TWI_TIMEOUT_enum {
	TWI_TIMEOUT_DISABLED_gc = (0x00 << 2), /* Bus Timeout Disabled */
	TWI_TIMEOUT_50US_gc     = (0x01 << 2), /* 50 Microseconds */
	TWI_TIMEOUT_100US_gc    = (0x02 << 2), /* 100 Microseconds */
	TWI_TIMEOUT_200US_gc    = (0x03 << 2), /* 200 Microseconds */
} TWI_TIMEOUT_t;

/*
--------------------------------------------------------------------------
USART - Universal Synchronous and Asynchronous Receiver and Transmitter
--------------------------------------------------------------------------
*/

/* Universal Synchronous and Asynchronous Receiver and Transmitter */
typedef struct USART_struct {
	register8_t RXDATAL; /* Receive Data Low Byte */
	register8_t RXDATAH; /* Receive Data High Byte */
	register8_t TXDATAL; /* Transmit Data Low Byte */
	register8_t TXDATAH; /* Transmit Data High Byte */
	register8_t STATUS;  /* Status */
	register8_t CTRLA;   /* Control A */
	register8_t CTRLB;   /* Control B */
	register8_t CTRLC;   /* Control C */
	_WORDREGISTER(BAUD); /* Baud Rate */
	register8_t reserved_1[1];
	register8_t DBGCTRL;  /* Debug Control */
	register8_t EVCTRL;   /* Event Control */
	register8_t TXPLCTRL; /* IRCOM Transmitter Pulse Length Control */
	register8_t RXPLCTRL; /* IRCOM Receiver Pulse Length Control */
	register8_t reserved_2[1];
} USART_t;

/* Character Size select */
typedef enum USART_CHSIZE_enum {
	USART_CHSIZE_5BIT_gc  = (0x00 << 0), /* Character size: 5 bit */
	USART_CHSIZE_6BIT_gc  = (0x01 << 0), /* Character size: 6 bit */
	USART_CHSIZE_7BIT_gc  = (0x02 << 0), /* Character size: 7 bit */
	USART_CHSIZE_8BIT_gc  = (0x03 << 0), /* Character size: 8 bit */
	USART_CHSIZE_9BITL_gc = (0x06 << 0), /* Character size: 9 bit read low byte first */
	USART_CHSIZE_9BITH_gc = (0x07 << 0), /* Character size: 9 bit read high byte first */
} USART_CHSIZE_t;

/* Communication Mode select */
typedef enum USART_CMODE_enum {
	USART_CMODE_ASYNCHRONOUS_gc = (0x00 << 6), /* Asynchronous Mode */
	USART_CMODE_SYNCHRONOUS_gc  = (0x01 << 6), /* Synchronous Mode */
	USART_CMODE_IRCOM_gc        = (0x02 << 6), /* Infrared Communication */
	USART_CMODE_MSPI_gc         = (0x03 << 6), /* Master SPI Mode */
} USART_CMODE_t;

/* Parity Mode select */
typedef enum USART_PMODE_enum {
	USART_PMODE_DISABLED_gc = (0x00 << 4), /* No Parity */
	USART_PMODE_EVEN_gc     = (0x02 << 4), /* Even Parity */
	USART_PMODE_ODD_gc      = (0x03 << 4), /* Odd Parity */
} USART_PMODE_t;

/* RS485 Mode internal transmitter select */
typedef enum USART_RS485_enum {
	USART_RS485_OFF_gc = (0x00 << 0), /* RS485 Mode disabled */
	USART_RS485_EXT_gc = (0x01 << 0), /* RS485 Mode External drive */
	USART_RS485_INT_gc = (0x02 << 0), /* RS485 Mode Internal drive */
} USART_RS485_t;

/* Receiver Mode select */
typedef enum USART_RXMODE_enum {
	USART_RXMODE_NORMAL_gc  = (0x00 << 1), /* Normal mode */
	USART_RXMODE_CLK2X_gc   = (0x01 << 1), /* CLK2x mode */
	USART_RXMODE_GENAUTO_gc = (0x02 << 1), /* Generic autobaud mode */
	USART_RXMODE_LINAUTO_gc = (0x03 << 1), /* LIN constrained autobaud mode */
} USART_RXMODE_t;

/* Stop Bit Mode select */
typedef enum USART_SBMODE_enum {
	USART_SBMODE_1BIT_gc = (0x00 << 3), /* 1 stop bit */
	USART_SBMODE_2BIT_gc = (0x01 << 3), /* 2 stop bits */
} USART_SBMODE_t;

/*
--------------------------------------------------------------------------
USERROW - User Row
--------------------------------------------------------------------------
*/

/* User Row */
typedef struct USERROW_struct {
	register8_t USERROW0;  /* User Row Byte 0 */
	register8_t USERROW1;  /* User Row Byte 1 */
	register8_t USERROW2;  /* User Row Byte 2 */
	register8_t USERROW3;  /* User Row Byte 3 */
	register8_t USERROW4;  /* User Row Byte 4 */
	register8_t USERROW5;  /* User Row Byte 5 */
	register8_t USERROW6;  /* User Row Byte 6 */
	register8_t USERROW7;  /* User Row Byte 7 */
	register8_t USERROW8;  /* User Row Byte 8 */
	register8_t USERROW9;  /* User Row Byte 9 */
	register8_t USERROW10; /* User Row Byte 10 */
	register8_t USERROW11; /* User Row Byte 11 */
	register8_t USERROW12; /* User Row Byte 12 */
	register8_t USERROW13; /* User Row Byte 13 */
	register8_t USERROW14; /* User Row Byte 14 */
	register8_t USERROW15; /* User Row Byte 15 */
	register8_t USERROW16; /* User Row Byte 16 */
	register8_t USERROW17; /* User Row Byte 17 */
	register8_t USERROW18; /* User Row Byte 18 */
	register8_t USERROW19; /* User Row Byte 19 */
	register8_t USERROW20; /* User Row Byte 20 */
	register8_t USERROW21; /* User Row Byte 21 */
	register8_t USERROW22; /* User Row Byte 22 */
	register8_t USERROW23; /* User Row Byte 23 */
	register8_t USERROW24; /* User Row Byte 24 */
	register8_t USERROW25; /* User Row Byte 25 */
	register8_t USERROW26; /* User Row Byte 26 */
	register8_t USERROW27; /* User Row Byte 27 */
	register8_t USERROW28; /* User Row Byte 28 */
	register8_t USERROW29; /* User Row Byte 29 */
	register8_t USERROW30; /* User Row Byte 30 */
	register8_t USERROW31; /* User Row Byte 31 */
	register8_t USERROW32; /* User Row Byte 32 */
	register8_t USERROW33; /* User Row Byte 33 */
	register8_t USERROW34; /* User Row Byte 34 */
	register8_t USERROW35; /* User Row Byte 35 */
	register8_t USERROW36; /* User Row Byte 36 */
	register8_t USERROW37; /* User Row Byte 37 */
	register8_t USERROW38; /* User Row Byte 38 */
	register8_t USERROW39; /* User Row Byte 39 */
	register8_t USERROW40; /* User Row Byte 40 */
	register8_t USERROW41; /* User Row Byte 41 */
	register8_t USERROW42; /* User Row Byte 42 */
	register8_t USERROW43; /* User Row Byte 43 */
	register8_t USERROW44; /* User Row Byte 44 */
	register8_t USERROW45; /* User Row Byte 45 */
	register8_t USERROW46; /* User Row Byte 46 */
	register8_t USERROW47; /* User Row Byte 47 */
	register8_t USERROW48; /* User Row Byte 48 */
	register8_t USERROW49; /* User Row Byte 49 */
	register8_t USERROW50; /* User Row Byte 50 */
	register8_t USERROW51; /* User Row Byte 51 */
	register8_t USERROW52; /* User Row Byte 52 */
	register8_t USERROW53; /* User Row Byte 53 */
	register8_t USERROW54; /* User Row Byte 54 */
	register8_t USERROW55; /* User Row Byte 55 */
	register8_t USERROW56; /* User Row Byte 56 */
	register8_t USERROW57; /* User Row Byte 57 */
	register8_t USERROW58; /* User Row Byte 58 */
	register8_t USERROW59; /* User Row Byte 59 */
	register8_t USERROW60; /* User Row Byte 60 */
	register8_t USERROW61; /* User Row Byte 61 */
	register8_t USERROW62; /* User Row Byte 62 */
	register8_t USERROW63; /* User Row Byte 63 */
} USERROW_t;

/*
--------------------------------------------------------------------------
VPORT - Virtual Ports
--------------------------------------------------------------------------
*/

/* Virtual Ports */
typedef struct VPORT_struct {
	register8_t DIR;      /* Data Direction */
	register8_t OUT;      /* Output Value */
	register8_t IN;       /* Input Value */
	register8_t INTFLAGS; /* Interrupt Flags */
} VPORT_t;

/*
--------------------------------------------------------------------------
VREF - Voltage reference
--------------------------------------------------------------------------
*/

/* Voltage reference */
typedef struct VREF_struct {
	register8_t CTRLA; /* Control A */
	register8_t CTRLB; /* Control B */
	register8_t CTRLC; /* Control C */
	register8_t CTRLD; /* Control D */
} VREF_t;

/* ADC0 reference select select */
typedef enum VREF_ADC0REFSEL_enum {
	VREF_ADC0REFSEL_0V55_gc = (0x00 << 4), /* Voltage reference at 0.55V */
	VREF_ADC0REFSEL_1V1_gc  = (0x01 << 4), /* Voltage reference at 1.1V */
	VREF_ADC0REFSEL_2V5_gc  = (0x02 << 4), /* Voltage reference at 2.5V */
	VREF_ADC0REFSEL_4V34_gc = (0x03 << 4), /* Voltage reference at 4.34V */
	VREF_ADC0REFSEL_1V5_gc  = (0x04 << 4), /* Voltage reference at 1.5V */
} VREF_ADC0REFSEL_t;

/* ADC1 reference select select */
typedef enum VREF_ADC1REFSEL_enum {
	VREF_ADC1REFSEL_0V55_gc = (0x00 << 4), /* Voltage reference at 0.55V */
	VREF_ADC1REFSEL_1V1_gc  = (0x01 << 4), /* Voltage reference at 1.1V */
	VREF_ADC1REFSEL_2V5_gc  = (0x02 << 4), /* Voltage reference at 2.5V */
	VREF_ADC1REFSEL_4V34_gc = (0x03 << 4), /* Voltage reference at 4.34V */
	VREF_ADC1REFSEL_1V5_gc  = (0x04 << 4), /* Voltage reference at 1.5V */
} VREF_ADC1REFSEL_t;

/* DAC0/AC0 reference select select */
typedef enum VREF_DAC0REFSEL_enum {
	VREF_DAC0REFSEL_0V55_gc = (0x00 << 0), /* Voltage reference at 0.55V */
	VREF_DAC0REFSEL_1V1_gc  = (0x01 << 0), /* Voltage reference at 1.1V */
	VREF_DAC0REFSEL_2V5_gc  = (0x02 << 0), /* Voltage reference at 2.5V */
	VREF_DAC0REFSEL_4V34_gc = (0x03 << 0), /* Voltage reference at 4.34V */
	VREF_DAC0REFSEL_1V5_gc  = (0x04 << 0), /* Voltage reference at 1.5V */
} VREF_DAC0REFSEL_t;

/* DAC1/AC1 reference select select */
typedef enum VREF_DAC1REFSEL_enum {
	VREF_DAC1REFSEL_0V55_gc = (0x00 << 0), /* Voltage reference at 0.55V */
	VREF_DAC1REFSEL_1V1_gc  = (0x01 << 0), /* Voltage reference at 1.1V */
	VREF_DAC1REFSEL_2V5_gc  = (0x02 << 0), /* Voltage reference at 2.5V */
	VREF_DAC1REFSEL_4V34_gc = (0x03 << 0), /* Voltage reference at 4.34V */
	VREF_DAC1REFSEL_1V5_gc  = (0x04 << 0), /* Voltage reference at 1.5V */
} VREF_DAC1REFSEL_t;

/* DAC2/AC2 reference select select */
typedef enum VREF_DAC2REFSEL_enum {
	VREF_DAC2REFSEL_0V55_gc = (0x00 << 0), /* Voltage reference at 0.55V */
	VREF_DAC2REFSEL_1V1_gc  = (0x01 << 0), /* Voltage reference at 1.1V */
	VREF_DAC2REFSEL_2V5_gc  = (0x02 << 0), /* Voltage reference at 2.5V */
	VREF_DAC2REFSEL_4V34_gc = (0x03 << 0), /* Voltage reference at 4.34V */
	VREF_DAC2REFSEL_1V5_gc  = (0x04 << 0), /* Voltage reference at 1.5V */
} VREF_DAC2REFSEL_t;

/*
--------------------------------------------------------------------------
WDT - Watch-Dog Timer
--------------------------------------------------------------------------
*/

/* Watch-Dog Timer */
typedef struct WDT_struct {
	register8_t CTRLA;  /* Control A */
	register8_t STATUS; /* Status */
} WDT_t;

/* Period select */
typedef enum WDT_PERIOD_enum {
	WDT_PERIOD_OFF_gc    = (0x00 << 0), /* Off */
	WDT_PERIOD_8CLK_gc   = (0x01 << 0), /* 8 cycles (8ms) */
	WDT_PERIOD_16CLK_gc  = (0x02 << 0), /* 16 cycles (16ms) */
	WDT_PERIOD_32CLK_gc  = (0x03 << 0), /* 32 cycles (32ms) */
	WDT_PERIOD_64CLK_gc  = (0x04 << 0), /* 64 cycles (64ms) */
	WDT_PERIOD_128CLK_gc = (0x05 << 0), /* 128 cycles (0.128s) */
	WDT_PERIOD_256CLK_gc = (0x06 << 0), /* 256 cycles (0.256s) */
	WDT_PERIOD_512CLK_gc = (0x07 << 0), /* 512 cycles (0.512s) */
	WDT_PERIOD_1KCLK_gc  = (0x08 << 0), /* 1K cycles (1.0s) */
	WDT_PERIOD_2KCLK_gc  = (0x09 << 0), /* 2K cycles (2.0s) */
	WDT_PERIOD_4KCLK_gc  = (0x0A << 0), /* 4K cycles (4.1s) */
	WDT_PERIOD_8KCLK_gc  = (0x0B << 0), /* 8K cycles (8.2s) */
} WDT_PERIOD_t;

/* Window select */
typedef enum WDT_WINDOW_enum {
	WDT_WINDOW_OFF_gc    = (0x00 << 4), /* Off */
	WDT_WINDOW_8CLK_gc   = (0x01 << 4), /* 8 cycles (8ms) */
	WDT_WINDOW_16CLK_gc  = (0x02 << 4), /* 16 cycles (16ms) */
	WDT_WINDOW_32CLK_gc  = (0x03 << 4), /* 32 cycles (32ms) */
	WDT_WINDOW_64CLK_gc  = (0x04 << 4), /* 64 cycles (64ms) */
	WDT_WINDOW_128CLK_gc = (0x05 << 4), /* 128 cycles (0.128s) */
	WDT_WINDOW_256CLK_gc = (0x06 << 4), /* 256 cycles (0.256s) */
	WDT_WINDOW_512CLK_gc = (0x07 << 4), /* 512 cycles (0.512s) */
	WDT_WINDOW_1KCLK_gc  = (0x08 << 4), /* 1K cycles (1.0s) */
	WDT_WINDOW_2KCLK_gc  = (0x09 << 4), /* 2K cycles (2.0s) */
	WDT_WINDOW_4KCLK_gc  = (0x0A << 4), /* 4K cycles (4.1s) */
	WDT_WINDOW_8KCLK_gc  = (0x0B << 4), /* 8K cycles (8.2s) */
} WDT_WINDOW_t;
/*
==========================================================================
IO Module Instances. Mapped to memory.
==========================================================================
*/

#define VPORTA (*(VPORT_t *)0x0000)    /* Virtual Ports */
#define VPORTB (*(VPORT_t *)0x0004)    /* Virtual Ports */
#define VPORTC (*(VPORT_t *)0x0008)    /* Virtual Ports */
#define RSTCTRL (*(RSTCTRL_t *)0x0040) /* Reset controller */
#define SLPCTRL (*(SLPCTRL_t *)0x0050) /* Sleep Controller */
#define CLKCTRL (*(CLKCTRL_t *)0x0060) /* Clock controller */
#define BOD (*(BOD_t *)0x0080)         /* Bod interface */
#define VREF (*(VREF_t *)0x00A0)       /* Voltage reference */
#define WDT (*(WDT_t *)0x0100)         /* Watch-Dog Timer */
#define CPUINT (*(CPUINT_t *)0x0110)   /* Interrupt Controller */
#define CRCSCAN (*(CRCSCAN_t *)0x0120) /* CRCSCAN */
#define RTC (*(RTC_t *)0x0140)         /* Real-Time Counter */
#define EVSYS (*(EVSYS_t *)0x0180)     /* Event System */
#define CCL (*(CCL_t *)0x01C0)         /* Configurable Custom Logic */
#define PORTMUX (*(PORTMUX_t *)0x0200) /* Port Multiplexer */
#define PORTA (*(PORT_t *)0x0400)      /* I/O Ports */
#define PORTB (*(PORT_t *)0x0420)      /* I/O Ports */
#define PORTC (*(PORT_t *)0x0440)      /* I/O Ports */
#define ADC0 (*(ADC_t *)0x0600)        /* Analog to Digital Converter */
#define ADC1 (*(ADC_t *)0x0640)        /* Analog to Digital Converter */
#define AC0 (*(AC_t *)0x0680)          /* Analog Comparator */
#define AC1 (*(AC_t *)0x0688)          /* Analog Comparator */
#define AC2 (*(AC_t *)0x0690)          /* Analog Comparator */
#define DAC0 (*(DAC_t *)0x06A0)        /* Digital to Analog Converter */
#define DAC1 (*(DAC_t *)0x06A8)        /* Digital to Analog Converter */
#define DAC2 (*(DAC_t *)0x06B0)        /* Digital to Analog Converter */
#define USART0 (*(USART_t *)0x0800)    /* Universal Synchronous and Asynchronous Receiver and Transmitter */
#define TWI0 (*(TWI_t *)0x0810)        /* Two-Wire Interface */
#define SPI0 (*(SPI_t *)0x0820)        /* Serial Peripheral Interface */
#define TCA0 (*(TCA_t *)0x0A00)        /* 16-bit Timer/Counter Type A */
#define TCB0 (*(TCB_t *)0x0A40)        /* 16-bit Timer Type B */
#define TCB1 (*(TCB_t *)0x0A50)        /* 16-bit Timer Type B */
#define TCD0 (*(TCD_t *)0x0A80)        /* Timer Counter D */
#define SYSCFG (*(SYSCFG_t *)0x0F00)   /* System Configuration Registers */
#define NVMCTRL (*(NVMCTRL_t *)0x1000) /* Non-volatile Memory Controller */
#define SIGROW (*(SIGROW_t *)0x1100)   /* Signature row */
#define FUSE (*(FUSE_t *)0x1280)       /* Fuses */
#define LOCKBIT (*(LOCKBIT_t *)0x128A) /* Lockbit */
#define USERROW (*(USERROW_t *)0x1300) /* User Row */

#endif /* !defined (__ASSEMBLER__) */

/* ========== Flattened fully qualified IO register names ========== */

/* VPORT (VPORTA) - Virtual Ports */
#define VPORTA_DIR _SFR_MEM8(0x0000)
#define VPORTA_OUT _SFR_MEM8(0x0001)
#define VPORTA_IN _SFR_MEM8(0x0002)
#define VPORTA_INTFLAGS _SFR_MEM8(0x0003)

/* VPORT (VPORTB) - Virtual Ports */
#define VPORTB_DIR _SFR_MEM8(0x0004)
#define VPORTB_OUT _SFR_MEM8(0x0005)
#define VPORTB_IN _SFR_MEM8(0x0006)
#define VPORTB_INTFLAGS _SFR_MEM8(0x0007)

/* VPORT (VPORTC) - Virtual Ports */
#define VPORTC_DIR _SFR_MEM8(0x0008)
#define VPORTC_OUT _SFR_MEM8(0x0009)
#define VPORTC_IN _SFR_MEM8(0x000A)
#define VPORTC_INTFLAGS _SFR_MEM8(0x000B)

/* GPIO - General Purpose IO */
#define GPIO_GPIOR0 _SFR_MEM8(0x001C)
#define GPIO_GPIOR1 _SFR_MEM8(0x001D)
#define GPIO_GPIOR2 _SFR_MEM8(0x001E)
#define GPIO_GPIOR3 _SFR_MEM8(0x001F)

/* Deprecated */
#define GPIO_GPIO0 _SFR_MEM8(0x001C)
#define GPIO_GPIO1 _SFR_MEM8(0x001D)
#define GPIO_GPIO2 _SFR_MEM8(0x001E)
#define GPIO_GPIO3 _SFR_MEM8(0x001F)

/* CPU - CPU */
#define CPU_CCP _SFR_MEM8(0x0034)
#define CPU_SPL _SFR_MEM8(0x003D)
#define CPU_SPH _SFR_MEM8(0x003E)
#define CPU_SREG _SFR_MEM8(0x003F)

/* RSTCTRL - Reset controller */
#define RSTCTRL_RSTFR _SFR_MEM8(0x0040)
#define RSTCTRL_SWRR _SFR_MEM8(0x0041)

/* SLPCTRL - Sleep Controller */
#define SLPCTRL_CTRLA _SFR_MEM8(0x0050)

/* CLKCTRL - Clock controller */
#define CLKCTRL_MCLKCTRLA _SFR_MEM8(0x0060)
#define CLKCTRL_MCLKCTRLB _SFR_MEM8(0x0061)
#define CLKCTRL_MCLKLOCK _SFR_MEM8(0x0062)
#define CLKCTRL_MCLKSTATUS _SFR_MEM8(0x0063)
#define CLKCTRL_OSC20MCTRLA _SFR_MEM8(0x0070)
#define CLKCTRL_OSC20MCALIBA _SFR_MEM8(0x0071)
#define CLKCTRL_OSC20MCALIBB _SFR_MEM8(0x0072)
#define CLKCTRL_OSC32KCTRLA _SFR_MEM8(0x0078)
#define CLKCTRL_XOSC32KCTRLA _SFR_MEM8(0x007C)

/* BOD - Bod interface */
#define BOD_CTRLA _SFR_MEM8(0x0080)
#define BOD_CTRLB _SFR_MEM8(0x0081)
#define BOD_VLMCTRLA _SFR_MEM8(0x0088)
#define BOD_INTCTRL _SFR_MEM8(0x0089)
#define BOD_INTFLAGS _SFR_MEM8(0x008A)
#define BOD_STATUS _SFR_MEM8(0x008B)

/* VREF - Voltage reference */
#define VREF_CTRLA _SFR_MEM8(0x00A0)
#define VREF_CTRLB _SFR_MEM8(0x00A1)
#define VREF_CTRLC _SFR_MEM8(0x00A2)
#define VREF_CTRLD _SFR_MEM8(0x00A3)

/* WDT - Watch-Dog Timer */
#define WDT_CTRLA _SFR_MEM8(0x0100)
#define WDT_STATUS _SFR_MEM8(0x0101)

/* CPUINT - Interrupt Controller */
#define CPUINT_CTRLA _SFR_MEM8(0x0110)
#define CPUINT_STATUS _SFR_MEM8(0x0111)
#define CPUINT_LVL0PRI _SFR_MEM8(0x0112)
#define CPUINT_LVL1VEC _SFR_MEM8(0x0113)

/* CRCSCAN - CRCSCAN */
#define CRCSCAN_CTRLA _SFR_MEM8(0x0120)
#define CRCSCAN_CTRLB _SFR_MEM8(0x0121)
#define CRCSCAN_STATUS _SFR_MEM8(0x0122)

/* RTC - Real-Time Counter */
#define RTC_CTRLA _SFR_MEM8(0x0140)
#define RTC_STATUS _SFR_MEM8(0x0141)
#define RTC_INTCTRL _SFR_MEM8(0x0142)
#define RTC_INTFLAGS _SFR_MEM8(0x0143)
#define RTC_TEMP _SFR_MEM8(0x0144)
#define RTC_DBGCTRL _SFR_MEM8(0x0145)
#define RTC_CLKSEL _SFR_MEM8(0x0147)
#define RTC_CNT _SFR_MEM16(0x0148)
#define RTC_CNTL _SFR_MEM8(0x0148)
#define RTC_CNTH _SFR_MEM8(0x0149)
#define RTC_PER _SFR_MEM16(0x014A)
#define RTC_PERL _SFR_MEM8(0x014A)
#define RTC_PERH _SFR_MEM8(0x014B)
#define RTC_CMP _SFR_MEM16(0x014C)
#define RTC_CMPL _SFR_MEM8(0x014C)
#define RTC_CMPH _SFR_MEM8(0x014D)
#define RTC_PITCTRLA _SFR_MEM8(0x0150)
#define RTC_PITSTATUS _SFR_MEM8(0x0151)
#define RTC_PITINTCTRL _SFR_MEM8(0x0152)
#define RTC_PITINTFLAGS _SFR_MEM8(0x0153)
#define RTC_PITDBGCTRL _SFR_MEM8(0x0155)

/* EVSYS - Event System */
#define EVSYS_ASYNCSTROBE _SFR_MEM8(0x0180)
#define EVSYS_SYNCSTROBE _SFR_MEM8(0x0181)
#define EVSYS_ASYNCCH0 _SFR_MEM8(0x0182)
#define EVSYS_ASYNCCH1 _SFR_MEM8(0x0183)
#define EVSYS_ASYNCCH2 _SFR_MEM8(0x0184)
#define EVSYS_ASYNCCH3 _SFR_MEM8(0x0185)
#define EVSYS_SYNCCH0 _SFR_MEM8(0x018A)
#define EVSYS_SYNCCH1 _SFR_MEM8(0x018B)
#define EVSYS_ASYNCUSER0 _SFR_MEM8(0x0192)
#define EVSYS_ASYNCUSER1 _SFR_MEM8(0x0193)
#define EVSYS_ASYNCUSER2 _SFR_MEM8(0x0194)
#define EVSYS_ASYNCUSER3 _SFR_MEM8(0x0195)
#define EVSYS_ASYNCUSER4 _SFR_MEM8(0x0196)
#define EVSYS_ASYNCUSER5 _SFR_MEM8(0x0197)
#define EVSYS_ASYNCUSER6 _SFR_MEM8(0x0198)
#define EVSYS_ASYNCUSER7 _SFR_MEM8(0x0199)
#define EVSYS_ASYNCUSER8 _SFR_MEM8(0x019A)
#define EVSYS_ASYNCUSER9 _SFR_MEM8(0x019B)
#define EVSYS_ASYNCUSER10 _SFR_MEM8(0x019C)
#define EVSYS_ASYNCUSER11 _SFR_MEM8(0x019D)
#define EVSYS_ASYNCUSER12 _SFR_MEM8(0x019E)
#define EVSYS_SYNCUSER0 _SFR_MEM8(0x01A2)
#define EVSYS_SYNCUSER1 _SFR_MEM8(0x01A3)

/* CCL - Configurable Custom Logic */
#define CCL_CTRLA _SFR_MEM8(0x01C0)
#define CCL_SEQCTRL0 _SFR_MEM8(0x01C1)
#define CCL_LUT0CTRLA _SFR_MEM8(0x01C5)
#define CCL_LUT0CTRLB _SFR_MEM8(0x01C6)
#define CCL_LUT0CTRLC _SFR_MEM8(0x01C7)
#define CCL_TRUTH0 _SFR_MEM8(0x01C8)
#define CCL_LUT1CTRLA _SFR_MEM8(0x01C9)
#define CCL_LUT1CTRLB _SFR_MEM8(0x01CA)
#define CCL_LUT1CTRLC _SFR_MEM8(0x01CB)
#define CCL_TRUTH1 _SFR_MEM8(0x01CC)

/* PORTMUX - Port Multiplexer */
#define PORTMUX_CTRLA _SFR_MEM8(0x0200)
#define PORTMUX_CTRLB _SFR_MEM8(0x0201)
#define PORTMUX_CTRLC _SFR_MEM8(0x0202)
#define PORTMUX_CTRLD _SFR_MEM8(0x0203)

/* PORT (PORTA) - I/O Ports */
#define PORTA_DIR _SFR_MEM8(0x0400)
#define PORTA_DIRSET _SFR_MEM8(0x0401)
#define PORTA_DIRCLR _SFR_MEM8(0x0402)
#define PORTA_DIRTGL _SFR_MEM8(0x0403)
#define PORTA_OUT _SFR_MEM8(0x0404)
#define PORTA_OUTSET _SFR_MEM8(0x0405)
#define PORTA_OUTCLR _SFR_MEM8(0x0406)
#define PORTA_OUTTGL _SFR_MEM8(0x0407)
#define PORTA_IN _SFR_MEM8(0x0408)
#define PORTA_INTFLAGS _SFR_MEM8(0x0409)
#define PORTA_PIN0CTRL _SFR_MEM8(0x0410)
#define PORTA_PIN1CTRL _SFR_MEM8(0x0411)
#define PORTA_PIN2CTRL _SFR_MEM8(0x0412)
#define PORTA_PIN3CTRL _SFR_MEM8(0x0413)
#define PORTA_PIN4CTRL _SFR_MEM8(0x0414)
#define PORTA_PIN5CTRL _SFR_MEM8(0x0415)
#define PORTA_PIN6CTRL _SFR_MEM8(0x0416)
#define PORTA_PIN7CTRL _SFR_MEM8(0x0417)

/* PORT (PORTB) - I/O Ports */
#define PORTB_DIR _SFR_MEM8(0x0420)
#define PORTB_DIRSET _SFR_MEM8(0x0421)
#define PORTB_DIRCLR _SFR_MEM8(0x0422)
#define PORTB_DIRTGL _SFR_MEM8(0x0423)
#define PORTB_OUT _SFR_MEM8(0x0424)
#define PORTB_OUTSET _SFR_MEM8(0x0425)
#define PORTB_OUTCLR _SFR_MEM8(0x0426)
#define PORTB_OUTTGL _SFR_MEM8(0x0427)
#define PORTB_IN _SFR_MEM8(0x0428)
#define PORTB_INTFLAGS _SFR_MEM8(0x0429)
#define PORTB_PIN0CTRL _SFR_MEM8(0x0430)
#define PORTB_PIN1CTRL _SFR_MEM8(0x0431)
#define PORTB_PIN2CTRL _SFR_MEM8(0x0432)
#define PORTB_PIN3CTRL _SFR_MEM8(0x0433)
#define PORTB_PIN4CTRL _SFR_MEM8(0x0434)
#define PORTB_PIN5CTRL _SFR_MEM8(0x0435)
#define PORTB_PIN6CTRL _SFR_MEM8(0x0436)
#define PORTB_PIN7CTRL _SFR_MEM8(0x0437)

/* PORT (PORTC) - I/O Ports */
#define PORTC_DIR _SFR_MEM8(0x0440)
#define PORTC_DIRSET _SFR_MEM8(0x0441)
#define PORTC_DIRCLR _SFR_MEM8(0x0442)
#define PORTC_DIRTGL _SFR_MEM8(0x0443)
#define PORTC_OUT _SFR_MEM8(0x0444)
#define PORTC_OUTSET _SFR_MEM8(0x0445)
#define PORTC_OUTCLR _SFR_MEM8(0x0446)
#define PORTC_OUTTGL _SFR_MEM8(0x0447)
#define PORTC_IN _SFR_MEM8(0x0448)
#define PORTC_INTFLAGS _SFR_MEM8(0x0449)
#define PORTC_PIN0CTRL _SFR_MEM8(0x0450)
#define PORTC_PIN1CTRL _SFR_MEM8(0x0451)
#define PORTC_PIN2CTRL _SFR_MEM8(0x0452)
#define PORTC_PIN3CTRL _SFR_MEM8(0x0453)
#define PORTC_PIN4CTRL _SFR_MEM8(0x0454)
#define PORTC_PIN5CTRL _SFR_MEM8(0x0455)
#define PORTC_PIN6CTRL _SFR_MEM8(0x0456)
#define PORTC_PIN7CTRL _SFR_MEM8(0x0457)

/* ADC (ADC0) - Analog to Digital Converter */
#define ADC0_CTRLA _SFR_MEM8(0x0600)
#define ADC0_CTRLB _SFR_MEM8(0x0601)
#define ADC0_CTRLC _SFR_MEM8(0x0602)
#define ADC0_CTRLD _SFR_MEM8(0x0603)
#define ADC0_CTRLE _SFR_MEM8(0x0604)
#define ADC0_SAMPCTRL _SFR_MEM8(0x0605)
#define ADC0_MUXPOS _SFR_MEM8(0x0606)
#define ADC0_COMMAND _SFR_MEM8(0x0608)
#define ADC0_EVCTRL _SFR_MEM8(0x0609)
#define ADC0_INTCTRL _SFR_MEM8(0x060A)
#define ADC0_INTFLAGS _SFR_MEM8(0x060B)
#define ADC0_DBGCTRL _SFR_MEM8(0x060C)
#define ADC0_TEMP _SFR_MEM8(0x060D)
#define ADC0_RES _SFR_MEM16(0x0610)
#define ADC0_RESL _SFR_MEM8(0x0610)
#define ADC0_RESH _SFR_MEM8(0x0611)
#define ADC0_WINLT _SFR_MEM16(0x0612)
#define ADC0_WINLTL _SFR_MEM8(0x0612)
#define ADC0_WINLTH _SFR_MEM8(0x0613)
#define ADC0_WINHT _SFR_MEM16(0x0614)
#define ADC0_WINHTL _SFR_MEM8(0x0614)
#define ADC0_WINHTH _SFR_MEM8(0x0615)
#define ADC0_CALIB _SFR_MEM8(0x0616)

/* ADC (ADC1) - Analog to Digital Converter */
#define ADC1_CTRLA _SFR_MEM8(0x0640)
#define ADC1_CTRLB _SFR_MEM8(0x0641)
#define ADC1_CTRLC _SFR_MEM8(0x0642)
#define ADC1_CTRLD _SFR_MEM8(0x0643)
#define ADC1_CTRLE _SFR_MEM8(0x0644)
#define ADC1_SAMPCTRL _SFR_MEM8(0x0645)
#define ADC1_MUXPOS _SFR_MEM8(0x0646)
#define ADC1_COMMAND _SFR_MEM8(0x0648)
#define ADC1_EVCTRL _SFR_MEM8(0x0649)
#define ADC1_INTCTRL _SFR_MEM8(0x064A)
#define ADC1_INTFLAGS _SFR_MEM8(0x064B)
#define ADC1_DBGCTRL _SFR_MEM8(0x064C)
#define ADC1_TEMP _SFR_MEM8(0x064D)
#define ADC1_RES _SFR_MEM16(0x0650)
#define ADC1_RESL _SFR_MEM8(0x0650)
#define ADC1_RESH _SFR_MEM8(0x0651)
#define ADC1_WINLT _SFR_MEM16(0x0652)
#define ADC1_WINLTL _SFR_MEM8(0x0652)
#define ADC1_WINLTH _SFR_MEM8(0x0653)
#define ADC1_WINHT _SFR_MEM16(0x0654)
#define ADC1_WINHTL _SFR_MEM8(0x0654)
#define ADC1_WINHTH _SFR_MEM8(0x0655)
#define ADC1_CALIB _SFR_MEM8(0x0656)

/* AC (AC0) - Analog Comparator */
#define AC0_CTRLA _SFR_MEM8(0x0680)
#define AC0_MUXCTRLA _SFR_MEM8(0x0682)
#define AC0_INTCTRL _SFR_MEM8(0x0686)
#define AC0_STATUS _SFR_MEM8(0x0687)

/* AC (AC1) - Analog Comparator */
#define AC1_CTRLA _SFR_MEM8(0x0688)
#define AC1_MUXCTRLA _SFR_MEM8(0x068A)
#define AC1_INTCTRL _SFR_MEM8(0x068E)
#define AC1_STATUS _SFR_MEM8(0x068F)

/* AC (AC2) - Analog Comparator */
#define AC2_CTRLA _SFR_MEM8(0x0690)
#define AC2_MUXCTRLA _SFR_MEM8(0x0692)
#define AC2_INTCTRL _SFR_MEM8(0x0696)
#define AC2_STATUS _SFR_MEM8(0x0697)

/* DAC (DAC0) - Digital to Analog Converter */
#define DAC0_CTRLA _SFR_MEM8(0x06A0)
#define DAC0_DATA _SFR_MEM8(0x06A1)

/* DAC (DAC1) - Digital to Analog Converter */
#define DAC1_CTRLA _SFR_MEM8(0x06A8)
#define DAC1_DATA _SFR_MEM8(0x06A9)

/* DAC (DAC2) - Digital to Analog Converter */
#define DAC2_CTRLA _SFR_MEM8(0x06B0)
#define DAC2_DATA _SFR_MEM8(0x06B1)

/* USART (USART0) - Universal Synchronous and Asynchronous Receiver and Transmitter */
#define USART0_RXDATAL _SFR_MEM8(0x0800)
#define USART0_RXDATAH _SFR_MEM8(0x0801)
#define USART0_TXDATAL _SFR_MEM8(0x0802)
#define USART0_TXDATAH _SFR_MEM8(0x0803)
#define USART0_STATUS _SFR_MEM8(0x0804)
#define USART0_CTRLA _SFR_MEM8(0x0805)
#define USART0_CTRLB _SFR_MEM8(0x0806)
#define USART0_CTRLC _SFR_MEM8(0x0807)
#define USART0_BAUD _SFR_MEM16(0x0808)
#define USART0_BAUDL _SFR_MEM8(0x0808)
#define USART0_BAUDH _SFR_MEM8(0x0809)
#define USART0_DBGCTRL _SFR_MEM8(0x080B)
#define USART0_EVCTRL _SFR_MEM8(0x080C)
#define USART0_TXPLCTRL _SFR_MEM8(0x080D)
#define USART0_RXPLCTRL _SFR_MEM8(0x080E)

/* TWI (TWI0) - Two-Wire Interface */
#define TWI0_CTRLA _SFR_MEM8(0x0810)
#define TWI0_DBGCTRL _SFR_MEM8(0x0812)
#define TWI0_MCTRLA _SFR_MEM8(0x0813)
#define TWI0_MCTRLB _SFR_MEM8(0x0814)
#define TWI0_MSTATUS _SFR_MEM8(0x0815)
#define TWI0_MBAUD _SFR_MEM8(0x0816)
#define TWI0_MADDR _SFR_MEM8(0x0817)
#define TWI0_MDATA _SFR_MEM8(0x0818)
#define TWI0_SCTRLA _SFR_MEM8(0x0819)
#define TWI0_SCTRLB _SFR_MEM8(0x081A)
#define TWI0_SSTATUS _SFR_MEM8(0x081B)
#define TWI0_SADDR _SFR_MEM8(0x081C)
#define TWI0_SDATA _SFR_MEM8(0x081D)
#define TWI0_SADDRMASK _SFR_MEM8(0x081E)

/* SPI (SPI0) - Serial Peripheral Interface */
#define SPI0_CTRLA _SFR_MEM8(0x0820)
#define SPI0_CTRLB _SFR_MEM8(0x0821)
#define SPI0_INTCTRL _SFR_MEM8(0x0822)
#define SPI0_INTFLAGS _SFR_MEM8(0x0823)
#define SPI0_DATA _SFR_MEM8(0x0824)

/* TCA (TCA0) - 16-bit Timer/Counter Type A */
#define TCA0_SINGLE_CTRLA _SFR_MEM8(0x0A00)
#define TCA0_SINGLE_CTRLB _SFR_MEM8(0x0A01)
#define TCA0_SINGLE_CTRLC _SFR_MEM8(0x0A02)
#define TCA0_SINGLE_CTRLD _SFR_MEM8(0x0A03)
#define TCA0_SINGLE_CTRLECLR _SFR_MEM8(0x0A04)
#define TCA0_SINGLE_CTRLESET _SFR_MEM8(0x0A05)
#define TCA0_SINGLE_CTRLFCLR _SFR_MEM8(0x0A06)
#define TCA0_SINGLE_CTRLFSET _SFR_MEM8(0x0A07)
#define TCA0_SINGLE_EVCTRL _SFR_MEM8(0x0A09)
#define TCA0_SINGLE_INTCTRL _SFR_MEM8(0x0A0A)
#define TCA0_SINGLE_INTFLAGS _SFR_MEM8(0x0A0B)
#define TCA0_SINGLE_DBGCTRL _SFR_MEM8(0x0A0E)
#define TCA0_SINGLE_TEMP _SFR_MEM8(0x0A0F)
#define TCA0_SINGLE_CNT _SFR_MEM16(0x0A20)
#define TCA0_SINGLE_PER _SFR_MEM16(0x0A26)
#define TCA0_SINGLE_CMP0 _SFR_MEM16(0x0A28)
#define TCA0_SINGLE_CMP1 _SFR_MEM16(0x0A2A)
#define TCA0_SINGLE_CMP2 _SFR_MEM16(0x0A2C)
#define TCA0_SINGLE_PERBUF _SFR_MEM16(0x0A36)
#define TCA0_SINGLE_CMP0BUF _SFR_MEM16(0x0A38)
#define TCA0_SINGLE_CMP1BUF _SFR_MEM16(0x0A3A)
#define TCA0_SINGLE_CMP2BUF _SFR_MEM16(0x0A3C)

#define TCA0_SPLIT_CTRLA _SFR_MEM8(0x0A00)
#define TCA0_SPLIT_CTRLB _SFR_MEM8(0x0A01)
#define TCA0_SPLIT_CTRLC _SFR_MEM8(0x0A02)
#define TCA0_SPLIT_CTRLD _SFR_MEM8(0x0A03)
#define TCA0_SPLIT_CTRLECLR _SFR_MEM8(0x0A04)
#define TCA0_SPLIT_CTRLESET _SFR_MEM8(0x0A05)
#define TCA0_SPLIT_INTCTRL _SFR_MEM8(0x0A0A)
#define TCA0_SPLIT_INTFLAGS _SFR_MEM8(0x0A0B)
#define TCA0_SPLIT_DBGCTRL _SFR_MEM8(0x0A0E)
#define TCA0_SPLIT_LCNT _SFR_MEM8(0x0A20)
#define TCA0_SPLIT_HCNT _SFR_MEM8(0x0A21)
#define TCA0_SPLIT_LPER _SFR_MEM8(0x0A26)
#define TCA0_SPLIT_HPER _SFR_MEM8(0x0A27)
#define TCA0_SPLIT_LCMP0 _SFR_MEM8(0x0A28)
#define TCA0_SPLIT_HCMP0 _SFR_MEM8(0x0A29)
#define TCA0_SPLIT_LCMP1 _SFR_MEM8(0x0A2A)
#define TCA0_SPLIT_HCMP1 _SFR_MEM8(0x0A2B)
#define TCA0_SPLIT_LCMP2 _SFR_MEM8(0x0A2C)
#define TCA0_SPLIT_HCMP2 _SFR_MEM8(0x0A2D)

/* TCB (TCB0) - 16-bit Timer Type B */
#define TCB0_CTRLA _SFR_MEM8(0x0A40)
#define TCB0_CTRLB _SFR_MEM8(0x0A41)
#define TCB0_EVCTRL _SFR_MEM8(0x0A44)
#define TCB0_INTCTRL _SFR_MEM8(0x0A45)
#define TCB0_INTFLAGS _SFR_MEM8(0x0A46)
#define TCB0_STATUS _SFR_MEM8(0x0A47)
#define TCB0_DBGCTRL _SFR_MEM8(0x0A48)
#define TCB0_TEMP _SFR_MEM8(0x0A49)
#define TCB0_CNT _SFR_MEM16(0x0A4A)
#define TCB0_CNTL _SFR_MEM8(0x0A4A)
#define TCB0_CNTH _SFR_MEM8(0x0A4B)
#define TCB0_CCMP _SFR_MEM16(0x0A4C)
#define TCB0_CCMPL _SFR_MEM8(0x0A4C)
#define TCB0_CCMPH _SFR_MEM8(0x0A4D)

/* TCB (TCB1) - 16-bit Timer Type B */
#define TCB1_CTRLA _SFR_MEM8(0x0A50)
#define TCB1_CTRLB _SFR_MEM8(0x0A51)
#define TCB1_EVCTRL _SFR_MEM8(0x0A54)
#define TCB1_INTCTRL _SFR_MEM8(0x0A55)
#define TCB1_INTFLAGS _SFR_MEM8(0x0A56)
#define TCB1_STATUS _SFR_MEM8(0x0A57)
#define TCB1_DBGCTRL _SFR_MEM8(0x0A58)
#define TCB1_TEMP _SFR_MEM8(0x0A59)
#define TCB1_CNT _SFR_MEM16(0x0A5A)
#define TCB1_CNTL _SFR_MEM8(0x0A5A)
#define TCB1_CNTH _SFR_MEM8(0x0A5B)
#define TCB1_CCMP _SFR_MEM16(0x0A5C)
#define TCB1_CCMPL _SFR_MEM8(0x0A5C)
#define TCB1_CCMPH _SFR_MEM8(0x0A5D)

/* TCD (TCD0) - Timer Counter D */
#define TCD0_CTRLA _SFR_MEM8(0x0A80)
#define TCD0_CTRLB _SFR_MEM8(0x0A81)
#define TCD0_CTRLC _SFR_MEM8(0x0A82)
#define TCD0_CTRLD _SFR_MEM8(0x0A83)
#define TCD0_CTRLE _SFR_MEM8(0x0A84)
#define TCD0_EVCTRLA _SFR_MEM8(0x0A88)
#define TCD0_EVCTRLB _SFR_MEM8(0x0A89)
#define TCD0_INTCTRL _SFR_MEM8(0x0A8C)
#define TCD0_INTFLAGS _SFR_MEM8(0x0A8D)
#define TCD0_STATUS _SFR_MEM8(0x0A8E)
#define TCD0_INPUTCTRLA _SFR_MEM8(0x0A90)
#define TCD0_INPUTCTRLB _SFR_MEM8(0x0A91)
#define TCD0_FAULTCTRL _SFR_MEM8(0x0A92)
#define TCD0_DLYCTRL _SFR_MEM8(0x0A94)
#define TCD0_DLYVAL _SFR_MEM8(0x0A95)
#define TCD0_DITCTRL _SFR_MEM8(0x0A98)
#define TCD0_DITVAL _SFR_MEM8(0x0A99)
#define TCD0_DBGCTRL _SFR_MEM8(0x0A9E)
#define TCD0_CAPTUREA _SFR_MEM16(0x0AA2)
#define TCD0_CAPTUREAL _SFR_MEM8(0x0AA2)
#define TCD0_CAPTUREAH _SFR_MEM8(0x0AA3)
#define TCD0_CAPTUREB _SFR_MEM16(0x0AA4)
#define TCD0_CAPTUREBL _SFR_MEM8(0x0AA4)
#define TCD0_CAPTUREBH _SFR_MEM8(0x0AA5)
#define TCD0_CMPASET _SFR_MEM16(0x0AA8)
#define TCD0_CMPASETL _SFR_MEM8(0x0AA8)
#define TCD0_CMPASETH _SFR_MEM8(0x0AA9)
#define TCD0_CMPACLR _SFR_MEM16(0x0AAA)
#define TCD0_CMPACLRL _SFR_MEM8(0x0AAA)
#define TCD0_CMPACLRH _SFR_MEM8(0x0AAB)
#define TCD0_CMPBSET _SFR_MEM16(0x0AAC)
#define TCD0_CMPBSETL _SFR_MEM8(0x0AAC)
#define TCD0_CMPBSETH _SFR_MEM8(0x0AAD)
#define TCD0_CMPBCLR _SFR_MEM16(0x0AAE)
#define TCD0_CMPBCLRL _SFR_MEM8(0x0AAE)
#define TCD0_CMPBCLRH _SFR_MEM8(0x0AAF)

/* SYSCFG - System Configuration Registers */
#define SYSCFG_REVID _SFR_MEM8(0x0F01)
#define SYSCFG_EXTBRK _SFR_MEM8(0x0F02)

/* NVMCTRL - Non-volatile Memory Controller */
#define NVMCTRL_CTRLA _SFR_MEM8(0x1000)
#define NVMCTRL_CTRLB _SFR_MEM8(0x1001)
#define NVMCTRL_STATUS _SFR_MEM8(0x1002)
#define NVMCTRL_INTCTRL _SFR_MEM8(0x1003)
#define NVMCTRL_INTFLAGS _SFR_MEM8(0x1004)
#define NVMCTRL_DATA _SFR_MEM16(0x1006)
#define NVMCTRL_DATAL _SFR_MEM8(0x1006)
#define NVMCTRL_DATAH _SFR_MEM8(0x1007)
#define NVMCTRL_ADDR _SFR_MEM16(0x1008)
#define NVMCTRL_ADDRL _SFR_MEM8(0x1008)
#define NVMCTRL_ADDRH _SFR_MEM8(0x1009)

/* SIGROW - Signature row */
#define SIGROW_DEVICEID0 _SFR_MEM8(0x1100)
#define SIGROW_DEVICEID1 _SFR_MEM8(0x1101)
#define SIGROW_DEVICEID2 _SFR_MEM8(0x1102)
#define SIGROW_SERNUM0 _SFR_MEM8(0x1103)
#define SIGROW_SERNUM1 _SFR_MEM8(0x1104)
#define SIGROW_SERNUM2 _SFR_MEM8(0x1105)
#define SIGROW_SERNUM3 _SFR_MEM8(0x1106)
#define SIGROW_SERNUM4 _SFR_MEM8(0x1107)
#define SIGROW_SERNUM5 _SFR_MEM8(0x1108)
#define SIGROW_SERNUM6 _SFR_MEM8(0x1109)
#define SIGROW_SERNUM7 _SFR_MEM8(0x110A)
#define SIGROW_SERNUM8 _SFR_MEM8(0x110B)
#define SIGROW_SERNUM9 _SFR_MEM8(0x110C)
#define SIGROW_TEMPSENSE0 _SFR_MEM8(0x1120)
#define SIGROW_TEMPSENSE1 _SFR_MEM8(0x1121)
#define SIGROW_OSC16ERR3V _SFR_MEM8(0x1122)
#define SIGROW_OSC16ERR5V _SFR_MEM8(0x1123)
#define SIGROW_OSC20ERR3V _SFR_MEM8(0x1124)
#define SIGROW_OSC20ERR5V _SFR_MEM8(0x1125)

/* FUSE - Fuses */
#define FUSE_WDTCFG _SFR_MEM8(0x1280)
#define FUSE_BODCFG _SFR_MEM8(0x1281)
#define FUSE_OSCCFG _SFR_MEM8(0x1282)
#define FUSE_TCD0CFG _SFR_MEM8(0x1284)
#define FUSE_SYSCFG0 _SFR_MEM8(0x1285)
#define FUSE_SYSCFG1 _SFR_MEM8(0x1286)
#define FUSE_APPEND _SFR_MEM8(0x1287)
#define FUSE_BOOTEND _SFR_MEM8(0x1288)

/* LOCKBIT - Lockbit */
#define LOCKBIT_LOCKBIT _SFR_MEM8(0x128A)

/* USERROW - User Row */
#define USERROW_USERROW0 _SFR_MEM8(0x1300)
#define USERROW_USERROW1 _SFR_MEM8(0x1301)
#define USERROW_USERROW2 _SFR_MEM8(0x1302)
#define USERROW_USERROW3 _SFR_MEM8(0x1303)
#define USERROW_USERROW4 _SFR_MEM8(0x1304)
#define USERROW_USERROW5 _SFR_MEM8(0x1305)
#define USERROW_USERROW6 _SFR_MEM8(0x1306)
#define USERROW_USERROW7 _SFR_MEM8(0x1307)
#define USERROW_USERROW8 _SFR_MEM8(0x1308)
#define USERROW_USERROW9 _SFR_MEM8(0x1309)
#define USERROW_USERROW10 _SFR_MEM8(0x130A)
#define USERROW_USERROW11 _SFR_MEM8(0x130B)
#define USERROW_USERROW12 _SFR_MEM8(0x130C)
#define USERROW_USERROW13 _SFR_MEM8(0x130D)
#define USERROW_USERROW14 _SFR_MEM8(0x130E)
#define USERROW_USERROW15 _SFR_MEM8(0x130F)
#define USERROW_USERROW16 _SFR_MEM8(0x1310)
#define USERROW_USERROW17 _SFR_MEM8(0x1311)
#define USERROW_USERROW18 _SFR_MEM8(0x1312)
#define USERROW_USERROW19 _SFR_MEM8(0x1313)
#define USERROW_USERROW20 _SFR_MEM8(0x1314)
#define USERROW_USERROW21 _SFR_MEM8(0x1315)
#define USERROW_USERROW22 _SFR_MEM8(0x1316)
#define USERROW_USERROW23 _SFR_MEM8(0x1317)
#define USERROW_USERROW24 _SFR_MEM8(0x1318)
#define USERROW_USERROW25 _SFR_MEM8(0x1319)
#define USERROW_USERROW26 _SFR_MEM8(0x131A)
#define USERROW_USERROW27 _SFR_MEM8(0x131B)
#define USERROW_USERROW28 _SFR_MEM8(0x131C)
#define USERROW_USERROW29 _SFR_MEM8(0x131D)
#define USERROW_USERROW30 _SFR_MEM8(0x131E)
#define USERROW_USERROW31 _SFR_MEM8(0x131F)
#define USERROW_USERROW32 _SFR_MEM8(0x1320)
#define USERROW_USERROW33 _SFR_MEM8(0x1321)
#define USERROW_USERROW34 _SFR_MEM8(0x1322)
#define USERROW_USERROW35 _SFR_MEM8(0x1323)
#define USERROW_USERROW36 _SFR_MEM8(0x1324)
#define USERROW_USERROW37 _SFR_MEM8(0x1325)
#define USERROW_USERROW38 _SFR_MEM8(0x1326)
#define USERROW_USERROW39 _SFR_MEM8(0x1327)
#define USERROW_USERROW40 _SFR_MEM8(0x1328)
#define USERROW_USERROW41 _SFR_MEM8(0x1329)
#define USERROW_USERROW42 _SFR_MEM8(0x132A)
#define USERROW_USERROW43 _SFR_MEM8(0x132B)
#define USERROW_USERROW44 _SFR_MEM8(0x132C)
#define USERROW_USERROW45 _SFR_MEM8(0x132D)
#define USERROW_USERROW46 _SFR_MEM8(0x132E)
#define USERROW_USERROW47 _SFR_MEM8(0x132F)
#define USERROW_USERROW48 _SFR_MEM8(0x1330)
#define USERROW_USERROW49 _SFR_MEM8(0x1331)
#define USERROW_USERROW50 _SFR_MEM8(0x1332)
#define USERROW_USERROW51 _SFR_MEM8(0x1333)
#define USERROW_USERROW52 _SFR_MEM8(0x1334)
#define USERROW_USERROW53 _SFR_MEM8(0x1335)
#define USERROW_USERROW54 _SFR_MEM8(0x1336)
#define USERROW_USERROW55 _SFR_MEM8(0x1337)
#define USERROW_USERROW56 _SFR_MEM8(0x1338)
#define USERROW_USERROW57 _SFR_MEM8(0x1339)
#define USERROW_USERROW58 _SFR_MEM8(0x133A)
#define USERROW_USERROW59 _SFR_MEM8(0x133B)
#define USERROW_USERROW60 _SFR_MEM8(0x133C)
#define USERROW_USERROW61 _SFR_MEM8(0x133D)
#define USERROW_USERROW62 _SFR_MEM8(0x133E)
#define USERROW_USERROW63 _SFR_MEM8(0x133F)

/*================== Bitfield Definitions ================== */

/* AC - Analog Comparator */
/* AC.CTRLA  bit masks and bit positions */
#define AC_ENABLE_bm 0x01       /* Enable bit mask. */
#define AC_ENABLE_bp 0          /* Enable bit position. */
#define AC_HYSMODE_gm 0x06      /* Hysteresis Mode group mask. */
#define AC_HYSMODE_gp 1         /* Hysteresis Mode group position. */
#define AC_HYSMODE0_bm (1 << 1) /* Hysteresis Mode bit 0 mask. */
#define AC_HYSMODE0_bp 1        /* Hysteresis Mode bit 0 position. */
#define AC_HYSMODE1_bm (1 << 2) /* Hysteresis Mode bit 1 mask. */
#define AC_HYSMODE1_bp 2        /* Hysteresis Mode bit 1 position. */
#define AC_LPMODE_bm 0x08       /* Low Power Mode bit mask. */
#define AC_LPMODE_bp 3          /* Low Power Mode bit position. */
#define AC_INTMODE_gm 0x30      /* Interrupt Mode group mask. */
#define AC_INTMODE_gp 4         /* Interrupt Mode group position. */
#define AC_INTMODE0_bm (1 << 4) /* Interrupt Mode bit 0 mask. */
#define AC_INTMODE0_bp 4        /* Interrupt Mode bit 0 position. */
#define AC_INTMODE1_bm (1 << 5) /* Interrupt Mode bit 1 mask. */
#define AC_INTMODE1_bp 5        /* Interrupt Mode bit 1 position. */
#define AC_OUTEN_bm 0x40        /* Output Buffer Enable bit mask. */
#define AC_OUTEN_bp 6           /* Output Buffer Enable bit position. */
#define AC_RUNSTDBY_bm 0x80     /* Run in Standby Mode bit mask. */
#define AC_RUNSTDBY_bp 7        /* Run in Standby Mode bit position. */

/* AC.MUXCTRLA  bit masks and bit positions */
#define AC_MUXNEG_gm 0x03      /* Negative Input MUX Selection group mask. */
#define AC_MUXNEG_gp 0         /* Negative Input MUX Selection group position. */
#define AC_MUXNEG0_bm (1 << 0) /* Negative Input MUX Selection bit 0 mask. */
#define AC_MUXNEG0_bp 0        /* Negative Input MUX Selection bit 0 position. */
#define AC_MUXNEG1_bm (1 << 1) /* Negative Input MUX Selection bit 1 mask. */
#define AC_MUXNEG1_bp 1        /* Negative Input MUX Selection bit 1 position. */
#define AC_MUXPOS_gm 0x18      /* Positive Input MUX Selection group mask. */
#define AC_MUXPOS_gp 3         /* Positive Input MUX Selection group position. */
#define AC_MUXPOS0_bm (1 << 3) /* Positive Input MUX Selection bit 0 mask. */
#define AC_MUXPOS0_bp 3        /* Positive Input MUX Selection bit 0 position. */
#define AC_MUXPOS1_bm (1 << 4) /* Positive Input MUX Selection bit 1 mask. */
#define AC_MUXPOS1_bp 4        /* Positive Input MUX Selection bit 1 position. */
#define AC_INVERT_bm 0x80      /* Invert AC Output bit mask. */
#define AC_INVERT_bp 7         /* Invert AC Output bit position. */

/* AC.INTCTRL  bit masks and bit positions */
#define AC_CMP_bm 0x01 /* Analog Comparator 0 Interrupt Enable bit mask. */
#define AC_CMP_bp 0    /* Analog Comparator 0 Interrupt Enable bit position. */

/* AC.STATUS  bit masks and bit positions */
/* AC_CMP  is already defined. */
#define AC_STATE_bm 0x10 /* Analog Comparator State bit mask. */
#define AC_STATE_bp 4    /* Analog Comparator State bit position. */

/* ADC - Analog to Digital Converter */
/* ADC.CTRLA  bit masks and bit positions */
#define ADC_ENABLE_bm 0x01  /* ADC Enable bit mask. */
#define ADC_ENABLE_bp 0     /* ADC Enable bit position. */
#define ADC_FREERUN_bm 0x02 /* ADC Freerun mode bit mask. */
#define ADC_FREERUN_bp 1    /* ADC Freerun mode bit position. */
#define ADC_RESSEL_bm 0x04  /* ADC Resolution bit mask. */
#define ADC_RESSEL_bp 2     /* ADC Resolution bit position. */
#define ADC_RUNSTBY_bm 0x80 /* Run standby mode bit mask. */
#define ADC_RUNSTBY_bp 7    /* Run standby mode bit position. */

/* ADC.CTRLB  bit masks and bit positions */
#define ADC_SAMPNUM_gm 0x07      /* Accumulation Samples group mask. */
#define ADC_SAMPNUM_gp 0         /* Accumulation Samples group position. */
#define ADC_SAMPNUM0_bm (1 << 0) /* Accumulation Samples bit 0 mask. */
#define ADC_SAMPNUM0_bp 0        /* Accumulation Samples bit 0 position. */
#define ADC_SAMPNUM1_bm (1 << 1) /* Accumulation Samples bit 1 mask. */
#define ADC_SAMPNUM1_bp 1        /* Accumulation Samples bit 1 position. */
#define ADC_SAMPNUM2_bm (1 << 2) /* Accumulation Samples bit 2 mask. */
#define ADC_SAMPNUM2_bp 2        /* Accumulation Samples bit 2 position. */

/* ADC.CTRLC  bit masks and bit positions */
#define ADC_PRESC_gm 0x07       /* Clock Pre-scaler group mask. */
#define ADC_PRESC_gp 0          /* Clock Pre-scaler group position. */
#define ADC_PRESC0_bm (1 << 0)  /* Clock Pre-scaler bit 0 mask. */
#define ADC_PRESC0_bp 0         /* Clock Pre-scaler bit 0 position. */
#define ADC_PRESC1_bm (1 << 1)  /* Clock Pre-scaler bit 1 mask. */
#define ADC_PRESC1_bp 1         /* Clock Pre-scaler bit 1 position. */
#define ADC_PRESC2_bm (1 << 2)  /* Clock Pre-scaler bit 2 mask. */
#define ADC_PRESC2_bp 2         /* Clock Pre-scaler bit 2 position. */
#define ADC_REFSEL_gm 0x30      /* Reference Selection group mask. */
#define ADC_REFSEL_gp 4         /* Reference Selection group position. */
#define ADC_REFSEL0_bm (1 << 4) /* Reference Selection bit 0 mask. */
#define ADC_REFSEL0_bp 4        /* Reference Selection bit 0 position. */
#define ADC_REFSEL1_bm (1 << 5) /* Reference Selection bit 1 mask. */
#define ADC_REFSEL1_bp 5        /* Reference Selection bit 1 position. */
#define ADC_SAMPCAP_bm 0x40     /* Sample Capacitance Selection bit mask. */
#define ADC_SAMPCAP_bp 6        /* Sample Capacitance Selection bit position. */
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
