lerouxb/minor-1/firmware/attiny3216/include/atmel_start_pins.h

/*
 * Code generated from START.
 *
 * This file will be overwritten when reconfiguring your START project.
 * Please copy examples or other code you want to keep to a separate file
 * to avoid losing it when reconfiguring.
 */
#ifndef ATMEL_START_PINS_H_INCLUDED
#define ATMEL_START_PINS_H_INCLUDED

#include <port.h>

/**
 * \brief Set SDA pull mode
 *
 * Configure pin to pull up, down or disable pull mode, supported pull
 * modes are defined by device used
 *
 * \param[in] pull_mode Pin pull mode
 */
static inline void SDA_set_pull_mode(const enum port_pull_mode pull_mode)
{
	PORTA_set_pin_pull_mode(1, pull_mode);
}

/**
 * \brief Set SDA data direction
 *
 * Select if the pin data direction is input, output or disabled.
 * If disabled state is not possible, this function throws an assert.
 *
 * \param[in] direction PORT_DIR_IN  = Data direction in
 *                      PORT_DIR_OUT = Data direction out
 *                      PORT_DIR_OFF = Disables the pin
 *                      (low power state)
 */
static inline void SDA_set_dir(const enum port_dir dir)
{
	PORTA_set_pin_dir(1, dir);
}

/**
 * \brief Set SDA input/sense configuration
 *
 * Enable/disable SDA digital input buffer and pin change interrupt,
 * select pin interrupt edge/level sensing mode
 *
 * \param[in] isc PORT_ISC_INTDISABLE_gc    = Iterrupt disabled but input buffer enabled
 *                PORT_ISC_BOTHEDGES_gc     = Sense Both Edges
 *                PORT_ISC_RISING_gc        = Sense Rising Edge
 *                PORT_ISC_FALLING_gc       = Sense Falling Edge
 *                PORT_ISC_INPUT_DISABLE_gc = Digital Input Buffer disabled
 *                PORT_ISC_LEVEL_gc         = Sense low Level
 */
static inline void SDA_set_isc(const PORT_ISC_t isc)
{
	PORTA_pin_set_isc(1, isc);
}

/**
 * \brief Set SDA inverted mode
 *
 * Enable or disable inverted I/O on a pin
 *
 * \param[in] inverted true  = I/O on SDA is inverted
 *                     false = I/O on SDA is not inverted
 */
static inline void SDA_set_inverted(const bool inverted)
{
	PORTA_pin_set_inverted(1, inverted);
}

/**
 * \brief Set SDA level
 *
 * Sets output level on a pin
 *
 * \param[in] level true  = Pin level set to "high" state
 *                  false = Pin level set to "low" state
 */
static inline void SDA_set_level(const bool level)
{
	PORTA_set_pin_level(1, level);
}

/**
 * \brief Toggle output level on SDA
 *
 * Toggle the pin level
 */
static inline void SDA_toggle_level()
{
	PORTA_toggle_pin_level(1);
}

/**
 * \brief Get level on SDA
 *
 * Reads the level on a pin
 */
static inline bool SDA_get_level()
{
	return PORTA_get_pin_level(1);
}

/**
 * \brief Set SCL pull mode
 *
 * Configure pin to pull up, down or disable pull mode, supported pull
 * modes are defined by device used
 *
 * \param[in] pull_mode Pin pull mode
 */
static inline void SCL_set_pull_mode(const enum port_pull_mode pull_mode)
{
	PORTA_set_pin_pull_mode(2, pull_mode);
}

/**
 * \brief Set SCL data direction
 *
 * Select if the pin data direction is input, output or disabled.
 * If disabled state is not possible, this function throws an assert.
 *
 * \param[in] direction PORT_DIR_IN  = Data direction in
 *                      PORT_DIR_OUT = Data direction out
 *                      PORT_DIR_OFF = Disables the pin
 *                      (low power state)
 */
static inline void SCL_set_dir(const enum port_dir dir)
{
	PORTA_set_pin_dir(2, dir);
}

/**
 * \brief Set SCL input/sense configuration
 *
 * Enable/disable SCL digital input buffer and pin change interrupt,
 * select pin interrupt edge/level sensing mode
 *
 * \param[in] isc PORT_ISC_INTDISABLE_gc    = Iterrupt disabled but input buffer enabled
 *                PORT_ISC_BOTHEDGES_gc     = Sense Both Edges
 *                PORT_ISC_RISING_gc        = Sense Rising Edge
 *                PORT_ISC_FALLING_gc       = Sense Falling Edge
 *                PORT_ISC_INPUT_DISABLE_gc = Digital Input Buffer disabled
 *                PORT_ISC_LEVEL_gc         = Sense low Level
 */
static inline void SCL_set_isc(const PORT_ISC_t isc)
{
	PORTA_pin_set_isc(2, isc);
}

/**
 * \brief Set SCL inverted mode
 *
 * Enable or disable inverted I/O on a pin
 *
 * \param[in] inverted true  = I/O on SCL is inverted
 *                     false = I/O on SCL is not inverted
 */
static inline void SCL_set_inverted(const bool inverted)
{
	PORTA_pin_set_inverted(2, inverted);
}

/**
 * \brief Set SCL level
 *
 * Sets output level on a pin
 *
 * \param[in] level true  = Pin level set to "high" state
 *                  false = Pin level set to "low" state
 */
static inline void SCL_set_level(const bool level)
{
	PORTA_set_pin_level(2, level);
}

/**
 * \brief Toggle output level on SCL
 *
 * Toggle the pin level
 */
static inline void SCL_toggle_level()
{
	PORTA_toggle_pin_level(2);
}

/**
 * \brief Get level on SCL
 *
 * Reads the level on a pin
 */
static inline bool SCL_get_level()
{
	return PORTA_get_pin_level(2);
}

/**
 * \brief Set KEYS pull mode
 *
 * Configure pin to pull up, down or disable pull mode, supported pull
 * modes are defined by device used
 *
 * \param[in] pull_mode Pin pull mode
 */
static inline void KEYS_set_pull_mode(const enum port_pull_mode pull_mode)
{
	PORTA_set_pin_pull_mode(4, pull_mode);
}

/**
 * \brief Set KEYS data direction
 *
 * Select if the pin data direction is input, output or disabled.
 * If disabled state is not possible, this function throws an assert.
 *
 * \param[in] direction PORT_DIR_IN  = Data direction in
 *                      PORT_DIR_OUT = Data direction out
 *                      PORT_DIR_OFF = Disables the pin
 *                      (low power state)
 */
static inline void KEYS_set_dir(const enum port_dir dir)
{
	PORTA_set_pin_dir(4, dir);
}

/**
 * \brief Set KEYS input/sense configuration
 *
 * Enable/disable KEYS digital input buffer and pin change interrupt,
 * select pin interrupt edge/level sensing mode
 *
 * \param[in] isc PORT_ISC_INTDISABLE_gc    = Iterrupt disabled but input buffer enabled
 *                PORT_ISC_BOTHEDGES_gc     = Sense Both Edges
 *                PORT_ISC_RISING_gc        = Sense Rising Edge
 *                PORT_ISC_FALLING_gc       = Sense Falling Edge
 *                PORT_ISC_INPUT_DISABLE_gc = Digital Input Buffer disabled
 *                PORT_ISC_LEVEL_gc         = Sense low Level
 */
static inline void KEYS_set_isc(const PORT_ISC_t isc)
{
	PORTA_pin_set_isc(4, isc);
}

/**
 * \brief Set KEYS inverted mode
 *
 * Enable or disable inverted I/O on a pin
 *
 * \param[in] inverted true  = I/O on KEYS is inverted
 *                     false = I/O on KEYS is not inverted
 */
static inline void KEYS_set_inverted(const bool inverted)
{
	PORTA_pin_set_inverted(4, inverted);
}

/**
 * \brief Set KEYS level
 *
 * Sets output level on a pin
 *
 * \param[in] level true  = Pin level set to "high" state
 *                  false = Pin level set to "low" state
 */
static inline void KEYS_set_level(const bool level)
{
	PORTA_set_pin_level(4, level);
}

/**
 * \brief Toggle output level on KEYS
 *
 * Toggle the pin level
 */
static inline void KEYS_toggle_level()
{
	PORTA_toggle_pin_level(4);
}

/**
 * \brief Get level on KEYS
 *
 * Reads the level on a pin
 */
static inline bool KEYS_get_level()
{
	return PORTA_get_pin_level(4);
}

/**
 * \brief Set DISABLE pull mode
 *
 * Configure pin to pull up, down or disable pull mode, supported pull
 * modes are defined by device used
 *
 * \param[in] pull_mode Pin pull mode
 */
static inline void DISABLE_set_pull_mode(const enum port_pull_mode pull_mode)
{
	PORTA_set_pin_pull_mode(5, pull_mode);
}

/**
 * \brief Set DISABLE data direction
 *
 * Select if the pin data direction is input, output or disabled.
 * If disabled state is not possible, this function throws an assert.
 *
 * \param[in] direction PORT_DIR_IN  = Data direction in
 *                      PORT_DIR_OUT = Data direction out
 *                      PORT_DIR_OFF = Disables the pin
 *                      (low power state)
 */
static inline void DISABLE_set_dir(const enum port_dir dir)
{
	PORTA_set_pin_dir(5, dir);
}

/**
 * \brief Set DISABLE input/sense configuration
 *
 * Enable/disable DISABLE digital input buffer and pin change interrupt,
 * select pin interrupt edge/level sensing mode
 *
 * \param[in] isc PORT_ISC_INTDISABLE_gc    = Iterrupt disabled but input buffer enabled
 *                PORT_ISC_BOTHEDGES_gc     = Sense Both Edges
 *                PORT_ISC_RISING_gc        = Sense Rising Edge
 *                PORT_ISC_FALLING_gc       = Sense Falling Edge
 *                PORT_ISC_INPUT_DISABLE_gc = Digital Input Buffer disabled
 *                PORT_ISC_LEVEL_gc         = Sense low Level
 */
static inline void DISABLE_set_isc(const PORT_ISC_t isc)
{
	PORTA_pin_set_isc(5, isc);
}

/**
 * \brief Set DISABLE inverted mode
 *
 * Enable or disable inverted I/O on a pin
 *
 * \param[in] inverted true  = I/O on DISABLE is inverted
 *                     false = I/O on DISABLE is not inverted
 */
static inline void DISABLE_set_inverted(const bool inverted)
{
	PORTA_pin_set_inverted(5, inverted);
}

/**
 * \brief Set DISABLE level
 *
 * Sets output level on a pin
 *
 * \param[in] level true  = Pin level set to "high" state
 *                  false = Pin level set to "low" state
 */
static inline void DISABLE_set_level(const bool level)
{
	PORTA_set_pin_level(5, level);
}

/**
 * \brief Toggle output level on DISABLE
 *
 * Toggle the pin level
 */
static inline void DISABLE_toggle_level()
{
	PORTA_toggle_pin_level(5);
}

/**
 * \brief Get level on DISABLE
 *
 * Reads the level on a pin
 */
static inline bool DISABLE_get_level()
{
	return PORTA_get_pin_level(5);
}

/**
 * \brief Set DAC pull mode
 *
 * Configure pin to pull up, down or disable pull mode, supported pull
 * modes are defined by device used
 *
 * \param[in] pull_mode Pin pull mode
 */
static inline void DAC_set_pull_mode(const enum port_pull_mode pull_mode)
{
	PORTA_set_pin_pull_mode(6, pull_mode);
}

/**
 * \brief Set DAC data direction
 *
 * Select if the pin data direction is input, output or disabled.
 * If disabled state is not possible, this function throws an assert.
 *
 * \param[in] direction PORT_DIR_IN  = Data direction in
 *                      PORT_DIR_OUT = Data direction out
 *                      PORT_DIR_OFF = Disables the pin
 *                      (low power state)
 */
static inline void DAC_set_dir(const enum port_dir dir)
{
	PORTA_set_pin_dir(6, dir);
}

/**
 * \brief Set DAC input/sense configuration
 *
 * Enable/disable DAC digital input buffer and pin change interrupt,
 * select pin interrupt edge/level sensing mode
 *
 * \param[in] isc PORT_ISC_INTDISABLE_gc    = Iterrupt disabled but input buffer enabled
 *                PORT_ISC_BOTHEDGES_gc     = Sense Both Edges
 *                PORT_ISC_RISING_gc        = Sense Rising Edge
 *                PORT_ISC_FALLING_gc       = Sense Falling Edge
 *                PORT_ISC_INPUT_DISABLE_gc = Digital Input Buffer disabled
 *                PORT_ISC_LEVEL_gc         = Sense low Level
 */
static inline void DAC_set_isc(const PORT_ISC_t isc)
{
	PORTA_pin_set_isc(6, isc);
}

/**
 * \brief Set DAC inverted mode
 *
 * Enable or disable inverted I/O on a pin
 *
 * \param[in] inverted true  = I/O on DAC is inverted
 *                     false = I/O on DAC is not inverted
 */
static inline void DAC_set_inverted(const bool inverted)
{
	PORTA_pin_set_inverted(6, inverted);
}

/**
 * \brief Set DAC level
 *
 * Sets output level on a pin
 *
 * \param[in] level true  = Pin level set to "high" state
 *                  false = Pin level set to "low" state
 */
static inline void DAC_set_level(const bool level)
{
	PORTA_set_pin_level(6, level);
}

/**
 * \brief Toggle output level on DAC
 *
 * Toggle the pin level
 */
static inline void DAC_toggle_level()
{
	PORTA_toggle_pin_level(6);
}

/**
 * \brief Get level on DAC
 *
 * Reads the level on a pin
 */
static inline bool DAC_get_level()
{
	return PORTA_get_pin_level(6);
}

/**
 * \brief Set LED pull mode
 *
 * Configure pin to pull up, down or disable pull mode, supported pull
 * modes are defined by device used
 *
 * \param[in] pull_mode Pin pull mode
 */
static inline void LED_set_pull_mode(const enum port_pull_mode pull_mode)
{
	PORTB_set_pin_pull_mode(0, pull_mode);
}

/**
 * \brief Set LED data direction
 *
 * Select if the pin data direction is input, output or disabled.
 * If disabled state is not possible, this function throws an assert.
 *
 * \param[in] direction PORT_DIR_IN  = Data direction in
 *                      PORT_DIR_OUT = Data direction out
 *                      PORT_DIR_OFF = Disables the pin
 *                      (low power state)
 */
static inline void LED_set_dir(const enum port_dir dir)
{
	PORTB_set_pin_dir(0, dir);
}

/**
 * \brief Set LED input/sense configuration
 *
 * Enable/disable LED digital input buffer and pin change interrupt,
 * select pin interrupt edge/level sensing mode
 *
 * \param[in] isc PORT_ISC_INTDISABLE_gc    = Iterrupt disabled but input buffer enabled
 *                PORT_ISC_BOTHEDGES_gc     = Sense Both Edges
 *                PORT_ISC_RISING_gc        = Sense Rising Edge
 *                PORT_ISC_FALLING_gc       = Sense Falling Edge
 *                PORT_ISC_INPUT_DISABLE_gc = Digital Input Buffer disabled
 *                PORT_ISC_LEVEL_gc         = Sense low Level
 */
static inline void LED_set_isc(const PORT_ISC_t isc)
{
	PORTB_pin_set_isc(0, isc);
}

/**
 * \brief Set LED inverted mode
 *
 * Enable or disable inverted I/O on a pin
 *
 * \param[in] inverted true  = I/O on LED is inverted
 *                     false = I/O on LED is not inverted
 */
static inline void LED_set_inverted(const bool inverted)
{
	PORTB_pin_set_inverted(0, inverted);
}

/**
 * \brief Set LED level
 *
 * Sets output level on a pin
 *
 * \param[in] level true  = Pin level set to "high" state
 *                  false = Pin level set to "low" state
 */
static inline void LED_set_level(const bool level)
{
	PORTB_set_pin_level(0, level);
}

/**
 * \brief Toggle output level on LED
 *
 * Toggle the pin level
 */
static inline void LED_toggle_level()
{
	PORTB_toggle_pin_level(0);
}

/**
 * \brief Get level on LED
 *
 * Reads the level on a pin
 */
static inline bool LED_get_level()
{
	return PORTB_get_pin_level(0);
}

/**
 * \brief Set TX pull mode
 *
 * Configure pin to pull up, down or disable pull mode, supported pull
 * modes are defined by device used
 *
 * \param[in] pull_mode Pin pull mode
 */
static inline void TX_set_pull_mode(const enum port_pull_mode pull_mode)
{
	PORTB_set_pin_pull_mode(2, pull_mode);
}

/**
 * \brief Set TX data direction
 *
 * Select if the pin data direction is input, output or disabled.
 * If disabled state is not possible, this function throws an assert.
 *
 * \param[in] direction PORT_DIR_IN  = Data direction in
 *                      PORT_DIR_OUT = Data direction out
 *                      PORT_DIR_OFF = Disables the pin
 *                      (low power state)
 */
static inline void TX_set_dir(const enum port_dir dir)
{
	PORTB_set_pin_dir(2, dir);
}

/**
 * \brief Set TX input/sense configuration
 *
 * Enable/disable TX digital input buffer and pin change interrupt,
 * select pin interrupt edge/level sensing mode
 *
 * \param[in] isc PORT_ISC_INTDISABLE_gc    = Iterrupt disabled but input buffer enabled
 *                PORT_ISC_BOTHEDGES_gc     = Sense Both Edges
 *                PORT_ISC_RISING_gc        = Sense Rising Edge
 *                PORT_ISC_FALLING_gc       = Sense Falling Edge
 *                PORT_ISC_INPUT_DISABLE_gc = Digital Input Buffer disabled
 *                PORT_ISC_LEVEL_gc         = Sense low Level
 */
static inline void TX_set_isc(const PORT_ISC_t isc)
{
	PORTB_pin_set_isc(2, isc);
}

/**
 * \brief Set TX inverted mode
 *
 * Enable or disable inverted I/O on a pin
 *
 * \param[in] inverted true  = I/O on TX is inverted
 *                     false = I/O on TX is not inverted
 */
static inline void TX_set_inverted(const bool inverted)
{
	PORTB_pin_set_inverted(2, inverted);
}

/**
 * \brief Set TX level
 *
 * Sets output level on a pin
 *
 * \param[in] level true  = Pin level set to "high" state
 *                  false = Pin level set to "low" state
 */
static inline void TX_set_level(const bool level)
{
	PORTB_set_pin_level(2, level);
}

/**
 * \brief Toggle output level on TX
 *
 * Toggle the pin level
 */
static inline void TX_toggle_level()
{
	PORTB_toggle_pin_level(2);
}

/**
 * \brief Get level on TX
 *
 * Reads the level on a pin
 */
static inline bool TX_get_level()
{
	return PORTB_get_pin_level(2);
}

/**
 * \brief Set RX pull mode
 *
 * Configure pin to pull up, down or disable pull mode, supported pull
 * modes are defined by device used
 *
 * \param[in] pull_mode Pin pull mode
 */
static inline void RX_set_pull_mode(const enum port_pull_mode pull_mode)
{
	PORTB_set_pin_pull_mode(3, pull_mode);
}

/**
 * \brief Set RX data direction
 *
 * Select if the pin data direction is input, output or disabled.
 * If disabled state is not possible, this function throws an assert.
 *
 * \param[in] direction PORT_DIR_IN  = Data direction in
 *                      PORT_DIR_OUT = Data direction out
 *                      PORT_DIR_OFF = Disables the pin
 *                      (low power state)
 */
static inline void RX_set_dir(const enum port_dir dir)
{
	PORTB_set_pin_dir(3, dir);
}

/**
 * \brief Set RX input/sense configuration
 *
 * Enable/disable RX digital input buffer and pin change interrupt,
 * select pin interrupt edge/level sensing mode
 *
 * \param[in] isc PORT_ISC_INTDISABLE_gc    = Iterrupt disabled but input buffer enabled
 *                PORT_ISC_BOTHEDGES_gc     = Sense Both Edges
 *                PORT_ISC_RISING_gc        = Sense Rising Edge
 *                PORT_ISC_FALLING_gc       = Sense Falling Edge
 *                PORT_ISC_INPUT_DISABLE_gc = Digital Input Buffer disabled
 *                PORT_ISC_LEVEL_gc         = Sense low Level
 */
static inline void RX_set_isc(const PORT_ISC_t isc)
{
	PORTB_pin_set_isc(3, isc);
}

/**
 * \brief Set RX inverted mode
 *
 * Enable or disable inverted I/O on a pin
 *
 * \param[in] inverted true  = I/O on RX is inverted
 *                     false = I/O on RX is not inverted
 */
static inline void RX_set_inverted(const bool inverted)
{
	PORTB_pin_set_inverted(3, inverted);
}

/**
 * \brief Set RX level
 *
 * Sets output level on a pin
 *
 * \param[in] level true  = Pin level set to "high" state
 *                  false = Pin level set to "low" state
 */
static inline void RX_set_level(const bool level)
{
	PORTB_set_pin_level(3, level);
}

/**
 * \brief Toggle output level on RX
 *
 * Toggle the pin level
 */
static inline void RX_toggle_level()
{
	PORTB_toggle_pin_level(3);
}

/**
 * \brief Get level on RX
 *
 * Reads the level on a pin
 */
static inline bool RX_get_level()
{
	return PORTB_get_pin_level(3);
}

/**
 * \brief Set BTN1 pull mode
 *
 * Configure pin to pull up, down or disable pull mode, supported pull
 * modes are defined by device used
 *
 * \param[in] pull_mode Pin pull mode
 */
static inline void BTN1_set_pull_mode(const enum port_pull_mode pull_mode)
{
	PORTC_set_pin_pull_mode(0, pull_mode);
}

/**
 * \brief Set BTN1 data direction
 *
 * Select if the pin data direction is input, output or disabled.
 * If disabled state is not possible, this function throws an assert.
 *
 * \param[in] direction PORT_DIR_IN  = Data direction in
 *                      PORT_DIR_OUT = Data direction out
 *                      PORT_DIR_OFF = Disables the pin
 *                      (low power state)
 */
static inline void BTN1_set_dir(const enum port_dir dir)
{
	PORTC_set_pin_dir(0, dir);
}

/**
 * \brief Set BTN1 input/sense configuration
 *
 * Enable/disable BTN1 digital input buffer and pin change interrupt,
 * select pin interrupt edge/level sensing mode
 *
 * \param[in] isc PORT_ISC_INTDISABLE_gc    = Iterrupt disabled but input buffer enabled
 *                PORT_ISC_BOTHEDGES_gc     = Sense Both Edges
 *                PORT_ISC_RISING_gc        = Sense Rising Edge
 *                PORT_ISC_FALLING_gc       = Sense Falling Edge
 *                PORT_ISC_INPUT_DISABLE_gc = Digital Input Buffer disabled
 *                PORT_ISC_LEVEL_gc         = Sense low Level
 */
static inline void BTN1_set_isc(const PORT_ISC_t isc)
{
	PORTC_pin_set_isc(0, isc);
}

/**
 * \brief Set BTN1 inverted mode
 *
 * Enable or disable inverted I/O on a pin
 *
 * \param[in] inverted true  = I/O on BTN1 is inverted
 *                     false = I/O on BTN1 is not inverted
 */
static inline void BTN1_set_inverted(const bool inverted)
{
	PORTC_pin_set_inverted(0, inverted);
}

/**
 * \brief Set BTN1 level
 *
 * Sets output level on a pin
 *
 * \param[in] level true  = Pin level set to "high" state
 *                  false = Pin level set to "low" state
 */
static inline void BTN1_set_level(const bool level)
{
	PORTC_set_pin_level(0, level);
}

/**
 * \brief Toggle output level on BTN1
 *
 * Toggle the pin level
 */
static inline void BTN1_toggle_level()
{
	PORTC_toggle_pin_level(0);
}

/**
 * \brief Get level on BTN1
 *
 * Reads the level on a pin
 */
static inline bool BTN1_get_level()
{
	return PORTC_get_pin_level(0);
}

/**
 * \brief Set BTN2 pull mode
 *
 * Configure pin to pull up, down or disable pull mode, supported pull
 * modes are defined by device used
 *
 * \param[in] pull_mode Pin pull mode
 */
static inline void BTN2_set_pull_mode(const enum port_pull_mode pull_mode)
{
	PORTC_set_pin_pull_mode(1, pull_mode);
}

/**
 * \brief Set BTN2 data direction
 *
 * Select if the pin data direction is input, output or disabled.
 * If disabled state is not possible, this function throws an assert.
 *
 * \param[in] direction PORT_DIR_IN  = Data direction in
 *                      PORT_DIR_OUT = Data direction out
 *                      PORT_DIR_OFF = Disables the pin
 *                      (low power state)
 */
static inline void BTN2_set_dir(const enum port_dir dir)
{
	PORTC_set_pin_dir(1, dir);
}

/**
 * \brief Set BTN2 input/sense configuration
 *
 * Enable/disable BTN2 digital input buffer and pin change interrupt,
 * select pin interrupt edge/level sensing mode
 *
 * \param[in] isc PORT_ISC_INTDISABLE_gc    = Iterrupt disabled but input buffer enabled
 *                PORT_ISC_BOTHEDGES_gc     = Sense Both Edges
 *                PORT_ISC_RISING_gc        = Sense Rising Edge
 *                PORT_ISC_FALLING_gc       = Sense Falling Edge
 *                PORT_ISC_INPUT_DISABLE_gc = Digital Input Buffer disabled
 *                PORT_ISC_LEVEL_gc         = Sense low Level
 */
static inline void BTN2_set_isc(const PORT_ISC_t isc)
{
	PORTC_pin_set_isc(1, isc);
}

/**
 * \brief Set BTN2 inverted mode
 *
 * Enable or disable inverted I/O on a pin
 *
 * \param[in] inverted true  = I/O on BTN2 is inverted
 *                     false = I/O on BTN2 is not inverted
 */
static inline void BTN2_set_inverted(const bool inverted)
{
	PORTC_pin_set_inverted(1, inverted);
}

/**
 * \brief Set BTN2 level
 *
 * Sets output level on a pin
 *
 * \param[in] level true  = Pin level set to "high" state
 *                  false = Pin level set to "low" state
 */
static inline void BTN2_set_level(const bool level)
{
	PORTC_set_pin_level(1, level);
}

/**
 * \brief Toggle output level on BTN2
 *
 * Toggle the pin level
 */
static inline void BTN2_toggle_level()
{
	PORTC_toggle_pin_level(1);
}

/**
 * \brief Get level on BTN2
 *
 * Reads the level on a pin
 */
static inline bool BTN2_get_level()
{
	return PORTC_get_pin_level(1);
}

/**
 * \brief Set BTN3 pull mode
 *
 * Configure pin to pull up, down or disable pull mode, supported pull
 * modes are defined by device used
 *
 * \param[in] pull_mode Pin pull mode
 */
static inline void BTN3_set_pull_mode(const enum port_pull_mode pull_mode)
{
	PORTC_set_pin_pull_mode(2, pull_mode);
}

/**
 * \brief Set BTN3 data direction
 *
 * Select if the pin data direction is input, output or disabled.
 * If disabled state is not possible, this function throws an assert.
 *
 * \param[in] direction PORT_DIR_IN  = Data direction in
 *                      PORT_DIR_OUT = Data direction out
 *                      PORT_DIR_OFF = Disables the pin
 *                      (low power state)
 */
static inline void BTN3_set_dir(const enum port_dir dir)
{
	PORTC_set_pin_dir(2, dir);
}

/**
 * \brief Set BTN3 input/sense configuration
 *
 * Enable/disable BTN3 digital input buffer and pin change interrupt,
 * select pin interrupt edge/level sensing mode
 *
 * \param[in] isc PORT_ISC_INTDISABLE_gc    = Iterrupt disabled but input buffer enabled
 *                PORT_ISC_BOTHEDGES_gc     = Sense Both Edges
 *                PORT_ISC_RISING_gc        = Sense Rising Edge
 *                PORT_ISC_FALLING_gc       = Sense Falling Edge
 *                PORT_ISC_INPUT_DISABLE_gc = Digital Input Buffer disabled
 *                PORT_ISC_LEVEL_gc         = Sense low Level
 */
static inline void BTN3_set_isc(const PORT_ISC_t isc)
{
	PORTC_pin_set_isc(2, isc);
}

/**
 * \brief Set BTN3 inverted mode
 *
 * Enable or disable inverted I/O on a pin
 *
 * \param[in] inverted true  = I/O on BTN3 is inverted
 *                     false = I/O on BTN3 is not inverted
 */
static inline void BTN3_set_inverted(const bool inverted)
{
	PORTC_pin_set_inverted(2, inverted);
}

/**
 * \brief Set BTN3 level
 *
 * Sets output level on a pin
 *
 * \param[in] level true  = Pin level set to "high" state
 *                  false = Pin level set to "low" state
 */
static inline void BTN3_set_level(const bool level)
{
	PORTC_set_pin_level(2, level);
}

/**
 * \brief Toggle output level on BTN3
 *
 * Toggle the pin level
 */
static inline void BTN3_toggle_level()
{
	PORTC_toggle_pin_level(2);
}

/**
 * \brief Get level on BTN3
 *
 * Reads the level on a pin
 */
static inline bool BTN3_get_level()
{
	return PORTC_get_pin_level(2);
}

#endif /* ATMEL_START_PINS_H_INCLUDED */
