lerouxb/minor-1/firmware/attiny3216/src/adc_basic.c

/**
 * \file
 *
 * \brief ADC Basic driver implementation.
 *
 (c) 2020 Microchip Technology Inc. and its subsidiaries.

    Subject to your compliance with these terms,you may use this software and
    any derivatives exclusively with Microchip products.It is your responsibility
    to comply with third party license terms applicable to your use of third party
    software (including open source software) that may accompany Microchip software.

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
    IN NO EVENT WILL MICROCHIP BE LIABLE FOR ANY INDIRECT, SPECIAL, PUNITIVE,
    INCIDENTAL OR CONSEQUENTIAL LOSS, DAMAGE, COST OR EXPENSE OF ANY KIND
    WHATSOEVER RELATED TO THE SOFTWARE, HOWEVER CAUSED, EVEN IF MICROCHIP HAS
    BEEN ADVISED OF THE POSSIBILITY OR THE DAMAGES ARE FORESEEABLE. TO THE
    FULLEST EXTENT ALLOWED BY LAW, MICROCHIP'S TOTAL LIABILITY ON ALL CLAIMS IN
    ANY WAY RELATED TO THIS SOFTWARE WILL NOT EXCEED THE AMOUNT OF FEES, IF ANY,
    THAT YOU HAVE PAID DIRECTLY TO MICROCHIP FOR THIS SOFTWARE.
 *
 */

/**
 * \defgroup doc_driver_adc_basic ADC Basic Driver
 * \ingroup doc_driver_adc
 *
 * \section doc_driver_adc_rev Revision History
 * - v0.0.0.1 Initial Commit
 *
 *@{
 */
#include <adc_basic.h>

/**
 * \brief Initialize ADC interface
 * If module is configured to disabled state, the clock to the ADC is disabled
 * if this is supported by the device's clock system.
 *
 * \return Initialization status.
 * \retval 0 the ADC init was successful
 * \retval 1 the ADC init was not successful
 */
int8_t ADC_0_init()
{

	// ADC0.CALIB = ADC_DUTYCYC_DUTY50_gc; /* 50% Duty cycle */

	// ADC0.CTRLB = ADC_SAMPNUM_ACC1_gc; /* 1 ADC sample */

	ADC0.CTRLC = ADC_PRESC_DIV4_gc      /* CLK_PER divided by 4 */
	             | ADC_REFSEL_VDDREF_gc /* VDD */
	             | 0 << ADC_SAMPCAP_bp; /* Sample Capacitance Selection: disabled */

	// ADC0.CTRLD = 0 << ADC_ASDV_bp /* Automatic Sampling Delay Variation: disabled */
	//		 | 0x0 << ADC_SAMPDLY_gp /* Sampling Delay Selection: 0x0 */
	//		 | ADC_INITDLY_DLY0_gc; /* Delay 0 CLK_ADC cycles */

	// ADC0.CTRLE = ADC_WINCM_NONE_gc; /* No Window Comparison */

	// ADC0.DBGCTRL = 0 << ADC_DBGRUN_bp; /* Debug run: disabled */

	// ADC0.EVCTRL = 0 << ADC_STARTEI_bp; /* Start Event Input Enable: disabled */

	// ADC0.INTCTRL = 0 << ADC_RESRDY_bp /* Result Ready Interrupt Enable: disabled */
	//		 | 0 << ADC_WCMP_bp; /* Window Comparator Interrupt Enable: disabled */

	ADC0.MUXPOS = ADC_MUXPOS_AIN4_gc; /* ADC input pin 4 */

	// ADC0.SAMPCTRL = 0x0 << ADC_SAMPLEN_gp; /* Sample length: 0x0 */

	// ADC0.WINHT = 0x0; /* Window Comparator High Threshold: 0x0 */

	// ADC0.WINLT = 0x0; /* Window Comparator Low Threshold: 0x0 */

	ADC0.CTRLA = 1 << ADC_ENABLE_bp     /* ADC Enable: enabled */
	             | 0 << ADC_FREERUN_bp  /* ADC Freerun mode: disabled */
	             | ADC_RESSEL_10BIT_gc  /* 10-bit mode */
	             | 0 << ADC_RUNSTBY_bp; /* Run standby mode: disabled */

	return 0;
}

/**
 * \brief Enable ADC_0
 * 1. If supported by the clock system, enables the clock to the ADC
 * 2. Enables the ADC module by setting the enable-bit in the ADC control register
 *
 * \return Nothing
 */
void ADC_0_enable()
{
	ADC0.CTRLA |= ADC_ENABLE_bm;
}
/**
 * \brief Disable ADC_0
 * 1. Disables the ADC module by clearing the enable-bit in the ADC control register
 * 2. If supported by the clock system, disables the clock to the ADC
 *
 * \return Nothing
 */
void ADC_0_disable()
{
	ADC0.CTRLA &= ~ADC_ENABLE_bm;
}

/**
 * \brief Start a conversion on ADC_0
 *
 * \param[in] channel The ADC channel to start conversion on
 *
 * \return Nothing
 */
void ADC_0_start_conversion(adc_0_channel_t channel)
{
	ADC0.MUXPOS  = channel;
	ADC0.COMMAND = ADC_STCONV_bm;
}

/**
 * \brief Check if the ADC conversion is done
 *
 * \return The status of ADC converison done check
 * \retval true The ADC conversion is done
 * \retval false The ADC converison is not done
 */
bool ADC_0_is_conversion_done()
{
	return (ADC0.INTFLAGS & ADC_RESRDY_bm);
}

/**
 * \brief Read a conversion result from ADC_0
 *
 * \return Conversion result read from the ADC_0 ADC module
 */
adc_result_t ADC_0_get_conversion_result(void)
{
	return (ADC0.RES);
}

/**
 * \brief Start a conversion, wait until ready, and return the conversion result
 *
 * \return Conversion result read from the ADC_0 ADC module
 */
adc_result_t ADC_0_get_conversion(adc_0_channel_t channel)
{
	adc_result_t res;

	ADC_0_start_conversion(channel);
	while (!ADC_0_is_conversion_done())
		;
	res = ADC_0_get_conversion_result();
	ADC0.INTFLAGS |= ADC_RESRDY_bm;
	return res;
}

/**
 * \brief Return the number of bits in the ADC conversion result
 *
 * \return The number of bits in the ADC conversion result
 */
uint8_t ADC_0_get_resolution()
{
	return (ADC0.CTRLA & ADC_RESSEL_bm) ? 8 : 10;
}
