lerouxb/minor-1/firmware/minor-1/notes.h

#ifndef NOTES_H
#define NOTES_H

// These notes are all frequency * 4294967296 / 25000
// Why 4294967296? Because we wrap around an unsigned 32-bit phase accumulator
// Why 25000? Because that's the sample rate.
// Therefore these note numbers are the "phase steps" per sample for each note.
const uint32_t notes[] = {
/* A0 */ 4724464,
/* A♯0/B♭0 */ 5005396,
/* B0 */ 5303032,
/* C1 */ 5618367,
/* C♯1/D♭1 */ 5952452,
/* D1 */ 6306404,
/* D♯1/E♭1 */ 6681401,
/* E1 */ 7078697,
/* F1 */ 7499619,
/* F♯1/G♭1 */ 7945569,
/* G1 */ 8418038,
/* G♯1/A♭1 */ 8918601,
/* A1 */ 9448928,
/* A♯1/B♭1 */ 10010791,
/* B1 */ 10606063,
/* C2 */ 11236732,
/* C♯2/D♭2 */ 11904904,
/* D2 */ 12612805,
/* D♯2/E♭2 */ 13362803,
/* E2 */ 14157396,
/* F2 */ 14999239,
/* F♯2/G♭2 */ 15891140,
/* G2 */ 16836076,
/* G♯2/A♭2 */ 17837205,
/* A2 */ 18897856,
/* A♯2/B♭2 */ 20021574,
/* B2 */ 21212122,
/* C3 */ 22473468,
/* C♯3/D♭3 */ 23809804,
/* D3 */ 25225614,
/* D♯3/E♭3 */ 26725606,
/* E3 */ 28314795,
/* F3 */ 29998474,
/* F♯3/G♭3 */ 31782277,
/* G3 */ 33672148,
/* G♯3/A♭3 */ 35674393,
/* A3 */ 37795712,
/* A♯3/B♭3 */ 40043166,
/* B3 */ 42424261,
/* C4 */ 44946936,
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
};

#endif
